devinhorowitz/solar-business-card/docs/solar-glow-drh-v2-mechanical.md

# SOLAR-GLOW · DRH — As-Built Mechanical Reference (v2-era; v3.0 deltas inline)

> **The v3.0 board files this doc names are no longer in `PCB/`** _(removed 2026-07-28; the current
> board is v4.0)_. They stay in git history —
> `git log --diff-filter=D -- PCB/solar-glow-drh-v3_0.kicad_pcb`, then
> `git show <sha>^:PCB/solar-glow-drh-v3_0.kicad_pcb`. The `enclosure/solar-glow-drh-v4_0-backshell-*`
> files are **not** affected by that PCB culling: they are still current and still what goes to the
> fab. _(They were named `…v3_0-backshell-…` until the 2026-08-19 rename; same geometry.)_

> **Superseded for the enclosure — read the v3.0 deltas.** The authoritative shell spec is now
> `enclosure/README.md` and the generator `enclosure/solar-glow-drh-v4_0-backshell-0p6b-brace-cad.py`; the board
> is **v3.0** (`PCB/solar-glow-drh-v3_0.kicad_pcb`). Since this doc was written the shell was built
> and aligned: the **mounting holes moved** (v3.0 positions below), the **floor is 1.00 mm** (0.95
> under a small U2 relief pocket), the **ribs are removed** (a resin diffuser brace carries center
> support), and the **overall height is 3.55 mm**.
> Use this doc for the board envelope, keepouts, and programming access; defer to `enclosure/README.md`
> for every shell number.

Every board dimension and coordinate here is read from the committed KiCad board (KiCad frame:
origin top-left, X across the 50.8 mm width, Y down the 88.9 mm length). Heights are datasheet
figures for the populated parts.

The board changed materially from the *original* shell modeled in `enclosure/` — **four supercaps
instead of two, no edge castellations, VQFN-28 not QFN-20, and an accelerometer tap instead of a
button.** That redesign is done: the shell (`solar-glow-drh-v4_0-backshell-*`, `v3_0`-named until
2026-08-19) is the result.
§8 lists what changed.

---

## 1. Board envelope

- **50.80 × 88.90 mm**, **0.6 mm** FR4, ENIG finish, matte-black soldermask.
- Rounded rectangle, **corner radius 3.0 mm** on all four corners (verified from Edge.Cuts).
- Front face is the show side (naked); the cover is a **back-only shell** that hugs the populated
  rear and presses over the board edge.

## 2. Mounting (4× M2)

Four plated through-holes, **2.2 mm drill**, all tied to **GND**:

| Hole | (x, y) |
|---|---|
| MH3 | (3.0, 3.0) |
| MH4 | (47.8, 3.0) |
| MH1 | (3.0, 85.9) |
| MH2 | (47.8, 85.9) |

All four corners, inset **3.0 mm from both edges** (v3.0 — concentric with the r3.0 corner fillets; was 3.5 mm from the long edges), pitch 44.80 × 82.90. The screws tie
the metal body to GND (intended — the shell becomes a grounded shield). M2 wants 3–4 mm of thread
engagement, so the **bosses must rise the full cavity height**; a thin floor cannot tap.

## 3. Which side is what

- **FRONT (naked, stays exposed):** the two solar cells, the central glow window (DRH monogram),
  and the four corner mount-hole entries. The shell does not cover the front.
- **BACK (the shell hugs this):** everything else — 4 supercaps, MCU, balancer, accelerometer,
  clamp, diodes, LEDs (reverse-mount), passives, the solder-bridge selectors, and the flat
  programming / breakout pads.

## 4. Front face — keep clear

| Feature | Center (x, y) | Size |
|---|---|---|
| PV1 solar cell | (25.4, 17.0) | ≈42 × 23 mm (SM141K06TF) |
| PV2 solar cell | (25.4, 71.9) | ≈42 × 23 mm |
| Glow window (DRH monogram) | (25.4, ~43.9) | x 14.95–35.85, y 40.8–47.0 (≈20.9 × 6.2 mm) bare-FR4 light window |

The two cells take the two ends; the glow window is dead center, backlit from the rear. Nothing on
the front is covered by the shell.

## 5. Back-side height stack (what the cavity must clear)

Two parts set the cavity; everything else clears under it.

| Part | What | Height | Center (x, y) |
|---|---|---|---|
| **U2** | balancer, SOIC-8 | **~1.75 mm (tallest)** | (28.5, 37.0) |
| **SC1–SC4** | WS17 supercaps | **1.7 mm** | see §6 |
| D1, D9 | blocking Schottky | ~1.1 mm | (44.0, 43.9), (43.5, 53.5) |
| U4 | TLV3011, SOT-23-6 | ~1.1 mm | (43.0, 49.0) |
| U3 | accelerometer, LGA-12 | ~1.0 mm | (20.0, 35.9) |
| U1 | MCU, VQFN-28 (4×4) | ~0.9 mm | (9.5, 40.9) |
| D2–D5 | LEDs, LA P47F (reverse-mount) | ~0.83 mm | row at y 43.9 |
| R / C | 1206 / 0805 | 0.6–0.7 mm | central band, y 32–55 |

→ The v3.0 shell uses a **general cavity of 1.80 mm** (cap-limited by the four 1.70 mm supercaps),
with a **0.05 mm relief pocket under U2** (1.75 mm) so the tallest part keeps its air while the floor
stays 1.00 mm — a *different* pocket than the old thin-skin one, and for a different reason
(engraving-stock floor, not a U2-limited cavity). See `enclosure/README.md`. **No through-hole
headers exist** (every connector is flat SMD), so nothing else stands
proud; the stack really is U2/cell-limited.

## 6. Big-part placement (what the shell works around)

**Supercaps — the area hogs** (4 × 28.5 × 17 mm ≈ 43% of the board), long axis along the 88.9 mm
length:

- **Top pair:** SC1 (15.5, 16.9), SC2 (35.3, 16.9) — occupy roughly x 7–44, y 2.6–31.2.
- **Bottom pair:** SC3 (15.5, 72.0), SC4 (35.3, 72.0) — occupy roughly x 7–44, y 57.8–86.3.

**Central electronics band (y ≈ 31–58):** MCU (U1, left), balancer (U2, center), accelerometer
(U3), clamp (Q1/U4/R7-9, right), the LED row + monogram (center), the SW2/SB/SJ selectors, the
passive field, and the breakout pads. This band is where all the routing and the optical heart live.

**Corners** (x 3.0 / 47.8, y 3.0 / 85.9): the four M2 holes (v3.0 positions), clear of the cells.

## 7. Optically-active zone — no pillars here

The LED row (D2–D5 at y 43.9) plus the glow window (x 15–36, y 40.8–47) is the optical heart.
Reverse-mount LEDs sit on the back and emit *through* the board to the front monogram, so an opaque
back shell behind them does not block the glow. But: **do not land support pillars on the LED pads
or the monogram traces**, and clear the ~0.83 mm LED bodies. Treat **x 15–36 / y 40–47 as a
no-pillar keepout**.

## 8. What changed from the shell in `enclosure/` (redesign, don't patch)

- **Four supercaps, not two.** The old CAD models one top pair plus a U2 pocket. v2.1 has four cells
  (both ends, §6). The pocket field, the SC pockets, and the pillar map must be re-laid-out for the
  four-cell footprint.
- **No edge castellations.** Verified: zero pads within 1.5 mm of the rim. The old CAD's biggest
  electrical hazard — press-fit walls shorting the right-edge VS/SDA/SCL castellations — **is gone.**
  Walls can press over the bare-FR4 edge with no edge-pad short.
- **U2 relief pocket (v3.0).** A 0.05 mm pocket under U2 lets the general floor run 1.00 mm while U2 keeps its 0.10 mm air; general cavity 1.80 mm. (Not the old U2-limited thin-skin pocket.) See `enclosure/README.md`.
- **VQFN-28, not QFN-20** (height-irrelevant at 0.9 mm; noted for accuracy).
- **No button.** The actuator is the accelerometer tap, which the metal back-plate *transmits*. No
  dome, no button hole, no cap-touch window.

## 9. Grounding & isolation (still applies)

The four M2 screws ground the body, so it is a defined-potential shield — good — but **any non-GND
copper the metal touches is a short.** Edge castellations are gone (§8), so the wall hazard is moot.
The remaining hazard is **support pillars pressing on the back**: soldermask (~20 µm) is a weak
insulator under load, and any exposed copper (untented vias, the VS pour) shorts to the GND body.
**Land pillars / lip on GND pour or bare laminate** — which the v3.0 shell does: its contacts land on
bare laminate (verified against the PCB), and the perimeter lip / back-frame was narrowed **1.50 →
1.00 mm** to clear the JP1/TP1 bench pads at the right edge. The **die-cut Kapton (~0.05 mm)** blanket
is therefore **dropped**, kept in reserve only for a future board that puts copper under a shell contact.

## 10. Programming access

The **TC2030** Tag-Connect pads (TC1) are on the **back** at (13.3, 16.9), tucked beside SC1, with
NPTH alignment/leg holes; pogo flashing is from the back. Decide up front: **flash before closing
the shell** (the pads sit in the program-before-mount dead space between the cells), or **cut a
TC2030 window** in the back shell for field re-flash. The backup UPDI header J1 (4.7, 38.4) is also
back-side flat pads.

## 11. Variants and open axes (the "enclosure(s)")

- **Material:** **Ti-6Al-4V Grade 5**, single material (yield ~880 MPa). The earlier 7075-T6 fallback
  is dropped — titanium's strength is what lets the floor run thin.
- **Machining (v3.0):** **fully 3-axis CNC-milled** (the photochemical-etch idea is dropped),
  bead-blast finish. **1.00 mm floor** (0.95 under the U2 relief pocket), no ribs — a resin diffuser
  brace carries center support; the window is backed by the brace's white diffuser face (reflector
  frame dropped); overall height 3.55 mm. Full CAD,
  callouts, and fab notes are in `enclosure/README.md`.
- **Floor thickness:** one shipping floor (**1.00 mm**, on the 0.6 mm board); the old 0.55 / 0.75 /
  standard / 0.2 mm-skin variants are retired. The floor is the single value re-issued to PCBWay's minimum.
- **Open vs enclosed:** with no castellations, the old "enclosed variant drops the edge bus"
  complication disappears — the enclosed build is simpler than it was.

## Cross-references

- **Shell design rules, material, machining, CAD knobs:** `enclosure/README.md`.
- **Why four cells / the rear real-estate logic / energy model:** `solar-glow-drh-design-notes.md` §4.
- **Exact pad and keepout geometry:** open `solar-glow-drh-v3_0.kicad_pcb` in KiCad.
