devinhorowitz/solar-business-card/docs/solar-glow-drh-v2-hardware.md

# SOLAR-GLOW · DRH — As-Built Hardware & Wiring Reference (v2-era; v3.0 deltas inline)

> **The v3.0 files this doc names are no longer in `PCB/`** _(removed 2026-07-28; the current board
> is v4.0)_. They are not lost — every revision stays in git history. To read one:
> `git log --diff-filter=D -- PCB/solar-glow-drh-v3_0.kicad_pcb` for the commit that removed it, then
> `git show <sha>^:PCB/solar-glow-drh-v3_0.kicad_pcb`. Nothing below is edited for v4; this is a
> historical record and the filenames are part of it.

> **v2-era doc — read the v3.0 deltas.** Written for v2.1 (+ the v2.2 NFC add). The current board is
> **v3.0 (2-layer)**; `PCB/solar-glow-drh-v3_0.kicad_pcb` governs and `firmware/README.md` carries the
> working pin map. Two v3.0 changes are applied inline here: the **LDRV/LED pin map was permuted**
> (pin 1/PA3 = LDRV1 → D2 … pin 26/PA0 = LDRV4 → D5 — the fan untangle), and the **stackup is 2-layer**
> (GND = full-board B.Cu pour, VS = routed B mesh; no inner planes), and the **NFC power-gate is now committed** (`U6` TPS22918 + `R14` 100 k `NFC_EN` pulldown — see the NFC note below). Net list, PORTMUX, and register
> values carry forward unchanged.

**The single source of truth for firmware.** Every line here is taken from the committed
`solar-glow-drh-v3_0.kicad_pcb` / `.kicad_sch` and cross-checked against the
AVR64DD32-28 datasheet (DS40002315), the ADXL367 datasheet, and the
SM141K06TF and SCPC parts. Where a register value is given, it is the value the firmware must
write to match what is physically routed.

**NFC subsystem — now fully committed (v2.2 → v3.0).** The board carries the NFC tag subsystem
(`U5` NT3H2211, `C8`, `C9` DNP, `R13`, and the etched antenna coil) on **PA6** (field-detect),
the **high-side load switch `U6` (TPS22918, SOT-23-6)** that power-gates `U5`'s VCC (`VNFC`)
from **PA7** (`NFC_EN`), and — added in the v3.0 R14 patch — a **100 kΩ pulldown `R14`** that
holds `NFC_EN` low whenever PA7 tristates (UPDI, reset, brown-out). All of it is committed on
`solar-glow-drh-v3_0.kicad_pcb`, and the NFC net wiring below has been **verified off the board
copper**: FD→PA6 ✓, `NFC_EN`→U6.ON ✓, `U5` Vcc→`VNFC` = U6.VOUT ✓, `R13`→VS (the always-on
rail, not the switched one) ✓, `R14` `NFC_EN`→GND ✓. The **U6 pin map is now verified against TI SLVSD76C (TPS22918 Rev C, then committed at
`datasheets/U6  TPS22918DBVR  $0.55.pdf` — culled 2026-08-01 with the other replaced-part sheets, git history; the doc for the then-ordered DBVR part; the -Q1 automotive
twin SLVSCZ8B has an identical pin table)** — and the check caught a real defect: the symbol had
**VIN/VOUT and GND/QOD transposed** (board said 1=VOUT, 2=QOD, 5=GND, 6=VIN; only ON=3 and
CT=4 were right). As routed it would have left U6 with no ground and fed VS into VOUT.
**Fixed on the board 2026-07-02**: pads renetted to TI truth (1=VIN, 2=GND, 3=ON,
4=CT-float, 5=QOD, 6=VOUT), schematic pin numbers corrected, QOD strapped to VOUT (internal
R_PD ≈ 25 Ω discharge — a TI-sanctioned config), CT left floating (also sanctioned), and the
local copper reworked to match. One open item: the **FD wake is bench-pending**
(scope PA6 on a real phone tap with VCC gated off). The NT3H2211 register/memory facts are
verified against the NTAG I²C plus datasheet (NT3H2111_2211 Rev 3.6).

MCU: **AVR64DD28**, 28-pin VQFN (footprint `solarglow:U1`). It sits on the **back** of the board.

---

## 1. MCU pin map (complete, as routed)

| Pad | Pin | Net | Function | Peripheral / firmware note |
|----:|---|---|---|---|
| 26 | **PA0** | `LDRV4` | LED (D5) cathode drive | **TCA0 WO0** — low-side sink, 150 Ω ballast |
| 27 | **PA1** | `LDRV3` | LED (D4) drive | **TCA0 WO1** |
| 28 | **PA2** | `LDRV2` | LED (D3) drive | **TCA0 WO2** |
| 1  | **PA3** | `LDRV1` | LED (D2) drive | **TCA0 WO3** |
| 2  | **PA4** | `PA4` | spare GPIO | spare (JP2 removed in v3.0 — no breakout) |
| 3  | **PA5** | `BTN` | reserved button | GPIO; only routed to a stub (the one DRC `track_dangling`); v3 hook |
| 4  | **PA6** | `FD` | NFC field-detect in (`U5`) | PORTA pin int, **falling**; field-powered (works VCC-off, §8.4); int pull-up on + ext 10k (`R13`) to VS — *v3.0-committed (R13→VS verified on copper); bench: scope a real tap* |
| 5  | **PA7** | `NFC_EN` | NFC VCC load-switch enable | output, **active-HIGH**, LOW = NFC off (default); **ext 100 k pulldown `R14` (v3.0)** holds it off while PA7 floats — *committed; U6 pin map verified per TI SLVSD76C, defect found + fixed 2026-07-02* |
| 6  | **PC0** | `PC0` | spare GPIO | spare (JP2 removed in v3.0) |
| 7  | **PC1** | `PC1` | spare GPIO | spare (JP2 removed in v3.0) |
| 8  | **PC2** | `SDA` | I²C data | **TWI0 host SDA** via `TWIROUTEA = ALT2`; 4.7 kΩ pull-up to VS |
| 9  | **PC3** | `SCL` | I²C clock | **TWI0 host SCL** via `TWIROUTEA = ALT2`; 4.7 kΩ pull-up to VS |
| 10 | **VDDIO2** | `VDDIO2` | PORTC I/O supply | tied to VS by SJ1 (0 Ω) — see §5 |
| 11 | **PD1** | — | free | unconnected (AIN1) |
| 12 | **PD2** | `VSENSE` | light / rail sense | **AIN2 (ADC)** + **AINP0 (AC0+)** → wake-on-light (§6) |
| 13 | **PD3** | — | free | unconnected (AIN3 / AINN0) |
| 14 | **PD4** | — | free | unconnected (AIN4) |
| 15 | **PD5** | — | free | unconnected (AIN5) |
| 16 | **PD6** | — | free | unconnected (AIN6 / AINP3 / DAC VOUT) |
| 17 | **PD7** | — | free | unconnected (VREFA / AIN7) |
| 18 | **VDD** | `VS` | core supply | the clamped rail, ≤ 3.60 V worst-case (≈3.50 typ) |
| 19 | **GND** | `GND` | ground | |
| 20 | **PF0** | `INT2` | accel INT2 input | PORTF pin interrupt |
| 21 | **PF1** | `INT1` | accel INT1 input | PORTF pin interrupt |
| 22 | **PF6/RST** | — | free | defaults to RESET; fuse to GPIO if ever needed |
| 23 | **UPDI** | `UPDI` | programming | TC2030 pad (TC1) + backup header J1 |
| 24 | **VDD** | `VS` | core supply | |
| 25 | **GND** | `GND` | ground | |
| EP | — | `GND` | exposed pad | thermal + ground |

**LED ↔ channel map** (note the off-by-one: D1/D9 are Schottkys, not LEDs):
`D2 → LDRV1 → PA3/WO3`, `D3 → LDRV2 → PA2/WO2`, `D4 → LDRV3 → PA1/WO1`, `D5 → LDRV4 → PA0/WO0` (v3.0 fan untangle).
Each LED: anode → `ANODE` (common) → **SW2** → VS; cathode → `Kn` → ballast (150 Ω) → `LDRVn` → MCU pin.

---

## 2. Nets & rails

| Net | What it is |
|---|---|
| `VIN` | PV1 (+) solar node, **before** blocking diode D1. ~0 V in the dark, rises with light. Feeds the VSENSE divider, D1 anode, and D10 (clamp-supply OR). |
| `VINB` | PV2 (+) solar node, before blocking diode D9, and D11 (clamp-supply OR). |
| `VS` | The storage rail (after D1/D9). = MCU VDD, accel VDD, LED anode source, supercap top. **Clamped ≤ 3.60 V worst-case** by the TLV3011 comparator + PNP shunt (U4/Q1). |
| `GND` | Ground — **full-board B.Cu pour** (`GND_B`) in v3.0 (was the In1 plane in v2.3), EP, the four M2 mount holes. |
| `MID` | Supercap series midpoint, balanced by U2 (ALD910025 dual SAB). |
| `CLBASE` / `CLREF` | Clamp internals — Q1 base (U4 open-drain OUT + R9 pullup) / VS sense-divider tap into U4 IN−. |
| `VCMP` | Clamp-comparator supply — **VIN OR-ed with VINB** through Schottkys D10/D11. Powers U4 only while a panel produces (0 draw in the dark); diode-OR so either panel alone keeps the clamp live under split shade. |
| `ANODE` | Common LED-anode node, switched by SW2. |
| `TINY` | Dim-mode node: LED anodes → VS through R12 (220 Ω) when SW2 = TINY. |
| `LDRV1‒4` | LED cathode drives → MCU PA0‒PA3. |
| `K2‒K5` | Individual LED-cathode-to-ballast nets. |
| `SDA` / `SCL` | I²C bus (accel `0x1D` + NFC tag `0x55`); tapped at `JP1.4`/`JP1.3` on the bench strip. |
| `INT1` / `INT2` | Accel interrupt lines → PF1 / PF0. |
| `VSENSE` | Light/rail sense → PD2. = VIN/2 (R5/R6 = 1 MΩ each), filtered by C5 (10 nF). |
| `PA4` / `PC0` / `PC1` | Spare GPIO (the v2-era JP2 breakout is gone — reserved, un-broken-out). |

Stackup: **v3.0 is 2-layer** (F / B) — GND = full-board B.Cu pour, VS = routed B mesh; 0.6 mm. (v2.3 fallback: 4-layer, F · In1 GND · In2 VS · B. v2.1 was 6-layer.)

---

## 3. Peripheral setup cheat-sheet (what firmware must configure)

**These are not defaults — they are the settings that match the routing.**

- **LED PWM — TCA0, split mode.**
  Keep `PORTMUX.TCAROUTEA = DEFAULT` (WO0‒WO3 already land on PA0‒PA3). Run TCA0 in
  **split mode** to get six 8-bit channels; WO0‒WO3 are the four LEDs, each with independent
  duty and a shared period. Set PA0‒PA3 as outputs. The 150 Ω ballast fixes the **peak**
  current (~9 mA on the clamped rail); PWM only trims the **average** below that, so brightness
  can be set freely but cannot exceed the ballast ceiling.
  *Gotcha:* the LEDs only light if **SW2 is bridged ON or TINY**. If SW2 = OFF (unbridged),
  no PWM will produce light — that's the hardware master switch.

- **I²C — TWI0, host mode.**
  **`PORTMUX.TWIROUTEA = ALT2`** (puts host SDA/SCL on PC2/PC3 — the default routes to
  PA2/PA3, which are LED pins). External 4.7 kΩ pull-ups are fitted, so don't enable internal
  ones. Bus is the accelerometer (`0x1D`) — and, since **v2.2**, the
  NFC tag `U5` (`0x55`); the two addresses don't clash, so no firmware change beyond
  talking to both. `U5` is reachable on I²C only while `NFC_EN` (PA7) powers it — it is
  gated **off** by default. FD (a pin interrupt on PA6) is separate from the bus, and is
  field-powered, so it works even with `U5`'s VCC gated off.

- **Accelerometer wake — PORTF pin interrupts.**
  Configure **PF1** (INT1) and **PF0** (INT2) as inputs with edge interrupts to match whatever
  the ADXL367 INT pins are programmed to assert (tap, double-tap, activity). These are the
  wake source for tap-to-glow.

- **Light sense / wake-on-light — PD2.**
  PD2 is both **AIN2** (ADC) and **AINP0** (AC0 positive input). See §6 for the validated
  options. The divider is VIN/2, so the ADC reading is `2 × VSENSE` ≈ VIN.

- **Free expansion ADC/analog** (all unconnected, available): PD1 (AIN1), PD3 (AIN3/AINN0),
  PD6 (AIN6/AINP3/DAC out), PD7 (VREFA/AIN7).

---

## 4. Devices on the board

**U3 — ADI ADXL367 accelerometer (the actuator; replaces the LIS2DH12 on backorder).**
- Interface: **I²C** (SCLK, pin 1 → GND = I²C mode). SDA = pin 2, SCL = pin 4.
- **Address: `0x1D`** 7-bit (ASEL, pin 3 → GND). 8-bit: write 0x3A / read 0x3B. IDs: DEVID_AD (0x00)
  = 0xAD, PART_ID (0x02) = 0xF7 (DEVID_MST 0x01 also reads 0x1D, coincidental with the bus address,
  not the same thing).
- Interrupts: **INT1 (pin 5) → PF1** (tap), **INT2 (pin 6) → PF0** (activity). Strapping is frozen
  in the schematic/PCB/BOM as of the ADXL367 swap.
- Supply Vs/Vsupply → VS; SCL → PC3, SDA → PC2 (MCU side); SDA/SCL pull-ups R10/R11 to VS. Decoupled by C6.
- Role: tap / double-tap / activity → INT → wakes the MCU. A tap is vibration, so the metal
  back-plate transmits it in the enclosed build. Single-vs-double tap is resolved in the
  ADXL367's own hardware window; the firmware reads STATUS_2 once (see `firmware/README.md`).

**U5 — NXP NT3H2211 (NTAG I²C plus, 2 KB) — NFC contact tag (v2.2).**
- Interface: **I²C target, address `0x55`** 7-bit (write 0xAA / read 0xAB); shares the TWI0
  bus with the accel (0x1D), no clash.
- **FD (field detect, pin 4) → PA6**, open-drain, ext 10 kΩ (`R13`) to VS: idles HIGH, pulls
  LOW on an NFC field → PA6 falling-edge interrupt wakes the MCU. FD is **field-powered**
  (§8.4), so this works even with `U5`'s VCC gated off; firmware also enables PA6's internal
  pull-up.
- Supply Vcc → **`VNFC` = `U6` (TPS22918) output**, gated by `NFC_EN` (PA7, active-HIGH; `R14` 100 k pulldown); U6 itself draws ISD ≈ 0.5 µA typ (3.5 µA max) from VS while off and IQ ≈ 8.3 µA while on (SLVSD76C §6.5); the
  switch input is on VS (clamped ≤ 3.60 V worst-case, inside the 3.6 V max). **Off by default** to kill
  the ~195 µA idle draw (datasheet Table 42); only powered around an MCU↔tag I²C access. `C8`
  (100 nF) decouples the switched VCC; `VOUT` (energy-harvest output) unconnected.
- Antenna: PCB coil on `LA`/`LB`, tuned to 13.56 MHz by the chip's internal 50 pF
  (`C9` = DNP trim). No firmware involvement in the radio.
- Role: a phone tap reads a contact **vCard** (RF-powered, so it reads with the cap flat) and
  the FD line wakes the glow. Firmware: `nfc.c` writes the NDEF into user memory from block 1;
  the factory CC (`E1 10 6D 00`) is left in place — block 0 is never written, as that would
  change the I²C address. *Net wiring verified off the v3.0 board copper (see the header note); FD-wake scope check still open.*

**LEDs — 4× ams OSRAM LA P47F (amber, reverse-mount).** Low-side driven on PA0‒PA3 (§1/§3),
150 Ω ballast each, anodes commoned to `ANODE` and switched by SW2.

**SW2 — LED master selector (3-pad solder bridge).** `ANODE` common; bridge to **VS = ON**
(full), to `TINY` = **TINY** (anodes → VS via R12 220 Ω, dim/long-runtime), unbridged = **OFF**
(true hardware off). Also `SB1‒SB4` are per-LED disable bridges in series with each ballast.

**Breakouts / programming.**
- `TC1` — TC2030 Tag-Connect (UPDI): hands-free flashing. `J1` — backup UPDI header.
- The v2-era `JP1`/`JP2` 2.54 mm breakout headers are **gone in v3.0**; `JP2` has no successor
  (PA4/PC0/PC1 stay reserved, un-broken-out). The `JP1` designator is **reused** for the bench pad
  strip below.

**Bench pad strip — `TP1` + `JP1` (new in v3.0).** Five bare SMD pads (1.7 mm square, ENIG,
2.54 mm pitch) in a column at x 48.4 on the **back**, in the margin between SC2's body edge
(x 43.8) and the card edge — the one strip the Ti shell interior clears (its lip was thinned
1.50 → 1.00 mm for exactly this; closed-shell clearance to the pads is 0.50 mm). Top to bottom:

| Pad | y | Net | Purpose |
|---|---|---|---|
| `TP1` | 12.00 | `VIN` | Solar-input node (pre-D1) — charge test / panel emulation |
| `JP1.1` | 14.54 | `GND` | Return (B.Cu pour) |
| `JP1.2` | 17.08 | `VS` | **Bench power injection** — 3.0–3.3 V, current-limited ~50 mA |
| `JP1.3` | 19.62 | `SCL` | I²C tap (via-in-pad stitches to the F-side run) |
| `JP1.4` | 22.16 | `SDA` | I²C tap (via-in-pad) |

No holes, nothing proud of the mask — clip, pogo, or tack a wire on for a bench session and
wick it off after. **Bench sequence:** inject at `JP1.2`/`JP1.1` → flash via `TC1` → functional
test → supercaps on → charge test at `TP1` → panels last. With the shell off the strip also
gives post-assembly I²C access to the NT3H2211 (`0x55`) and ADXL367 (`0x1D`); with the shell
on nothing is probe-able anyway, by design.

---

## 5. Power & sensing

- **Harvest:** 2× SM141K06TF (Voc 4.15 V, Vmp 3.35 V, Isc 58.6 mA at 1 sun), in parallel,
  each behind its own Schottky — **PV1 → D1 → VS** and **PV2 → D9 → VS** (both MMSD301T1G) —
  so a shadow on one panel can't back-drive the other.
- **Storage:** 4× SCHURTER WS17 (P/N 3-153-438), wired **2P2S → 1 F @ 5.5 V ≈ 15 J**, on one
  node balanced by **U2 (ALD910025)** at the midpoint. Cell rating is **−40 to +85 °C**; each
  cell sees only VS/2 (≈1.75 V, far under the 2.75 V rating), so voltage is never the limit,
  but high heat is: leakage climbs and calendar life roughly halves per 10 °C over 85 °C.
  **Hot-car caveat** — a matte-black card on a sunlit dash can self-heat to 80–90 °C, at/above
  the cell rating; this ages the supercaps and speeds self-discharge (it does **not** damage
  the ICs — see the clamp note). An 85 °C+ / 105 °C cell is the fix if hot storage is a goal.
- **Rail clamp:** **TLV3011 comparator + on-chip 1.242 V ref (U4)** + PNP (Q1) shunt holds
  **VS ≤ 3.60 V worst-case** (≈3.50 V typ) so the accelerometer **and** the NFC tag stay at/under
  their shared 3.6 V operating max. Divider **R7 (6.81 M) / R8 (3.74 M)** sets the trip via
  VS = 1.242·(1+R7/R8); it sits on VS (must — both panels feed VS through separate diodes).
  R7/R8 were chosen to put the **worst-case** clamp (ref ±1% + 100 ppm/°C + resistor ±1%) right
  on 3.60 V, wringing out maximum storage energy (E ∝ V²) while staying under the datasheet max. The divider is high-impedance (6.81 M / 3.74 M ≈ 10.5 MΩ) — the **only** continuous passive drain off the supercaps, ~**0.33 µA** at 3.5 V. This high-Z is only possible because the TLV3011’s ±10 pA input bias makes the resistor offset negligible; the old TLV431’s 0.5 µA Iref would have added ~0.9 V here, which is why it was forced to a low-impedance 1.8 M / 1.0 M divider (≈1.24 µA).
  Open-drain OUT drives Q1 through the R9 pullup. **Comparator power:** U4's V+ is fed from
  **VCMP = VIN OR-ed with VINB** through two Schottkys (D10/D11), **not** from VS — so U4's
  ~2.8 µA quiescent is pulled from the solar cells only while they produce and is **zero in the
  dark** (the clamp can only ever need to act while charging). The OR (vs VIN alone) keeps the
  clamp live under **split illumination** — a shadowed panel can't leave VS unclamped while the
  other charges it. R9, the divider, and Q1 stay on VS (R9 *must*, or Q1 turns on in the dark and
  shorts VS). Safe because the TLV3011**B**'s fail-safe inputs and its output-pullup-independent-
  of-supply rating mean an unpowered U4 (R9 holding Q1's base at VS) neither back-powers nor
  leaks through the chip. **C10** (100 nF) decouples VCMP at U4's V+ — not strictly required (VCMP carries no switching load; the Q1-drive transient sinks from VS through R9, and the comparator has hysteresis), but standard local decoupling. *(Supersedes the earlier TLV431 divider, whose
  0.5 µA Iref across a 1.8 M top resistor pushed the real clamp to ~3.74 V typ / ~4.5 V worst —
  a latent over-voltage the TLV3011's ±10 pA input bias eliminates.)* **Hot-car:** at 85–105 °C
  worst-case creeps to ~3.61–3.65 V, still ~1 V under both parts' 4.6/4.8 V absolute-max damage
  line, so no damage — only a brief excursion outside the guaranteed operating window.
- **VDDIO2 = VS** via SJ1, so PORTC runs at the rail and **MVIO is unused** (no separate I/O
  voltage). The MVIO fuse `SYSCFG1.MVSYSCFG` should be set to **SINGLE** to match (factory
  default is DUAL; DUAL also works since VDDIO2 sits at a valid voltage, but SINGLE is the
  intent). PORTC pins are valid up to VS. See the firmware README "Fuses" section.
- **Sense:** `VSENSE = VIN / 2` (R5/R6 = 1 MΩ, C5 = 10 nF, ~5 ms filter) into PD2. Reads the
  *solar input*, not the stored rail — see §6.

---

## 6. Wake-on-light — validated, viable as wired (no board change)

> **Firmware reconciliation (read first).** The firmware implements **path B
> only**. **Path A (AC0 instant wake) was found non-viable on this silicon** once
> verified against the datasheet: the AC0 interrupt and flags do not update while
> `CLK_PER` is stopped, and Table 13-4 does not list the AC as a Standby or
> Power-Down wake source, so an AC0 wake would silently never fire. The **wiring
> below is still correct** and path B works exactly as described; what is stale is
> the option-A recommendation (AC0 can't wake from Standby on this part). The
> current/darkness estimates have moved twice: the firmware bring-up found the old
> ~2 µA accel figure was really ~10 µA for the click-armed LIS2DH12, and the ADXL367
> swap then dropped it to ~0.89 µA (standby ~2.7 µA). The authoritative wake/power
> model lives in **`firmware/README.md` ("Power notes / wake architecture")**.

Confirmed electrically this revision. The divider sits on **VIN (before D1)**, so VSENSE
collapses to ~0 V in the dark and rises with light; **PD2 = AINP0** is a real AC0 input and
**AIN2** is a real ADC input. Signal swing: ~0 V dark → ~1.2–2.1 V in light (dim-indoor to
sun), against an easily-set threshold near ~0.4 V. AC0 input range is −0.2 V…VDD, so VSENSE
fits. Two implementations, same wiring — choose per use:

**A) AC0 comparator — instant wake. [NOT VIABLE — see the reconciliation note above; kept as the record of why it was considered.]**
- AC0 `MUXPOS = AINP0` (PD2); `MUXNEG = DACREF`; set threshold `DACREF × VREF` ≈ 0.4 V.
- Enable hysteresis (10/25/50 mV) so a flickering source doesn't chatter the interrupt.
- `CTRLA.RUNSTDBY = 1`, sleep in **Standby**; the AC0 CMP interrupt wakes the core the moment
  light appears. Use `CTRLA.POWER = 0x2` (slowest, plenty fast for light) ≈ **~12 µA** standing.
- Dark tolerance (as originally estimated): AC0 (~12 µA) + accel (~2 µA) + standby (~3 µA)
  ≈ ~16 µA. *The AC0 assumption is wrong* — A does not work at all on this part. The accel
  figure has since settled at ~0.89 µA (ADXL367), so total dark standby is ~2.7 µA — see the
  README for the current model.

**B) RTC/PIT poll + ADC — dark-tolerant.**
- Sleep in **Power-Down**; wake every ~1–2 s off the internal-ULP RTC/PIT; ADC-sample PD2
  (AIN2); escalate to full wake only when the reading clears the light threshold.
- Detection latency ~1–2 s. (The "~1–3 µA → ~5–7 days" originally written here omitted the
  always-on accelerometer; with the ADXL367 at ~0.89 µA the standing draw is ~2.7 µA total —
  no longer accel-dominated — so darkness survival is back on the order of **days** — see README.)
- Note: in the deepest Power-Down the AC0 is off, so this is the only wake-on-light that works
  in that mode — and it's the better fit for "card sat in a drawer."

Both recharge instantly when light returns. **B is the baseline and the only viable
wake-on-light path.** Instant response is not lost: the accelerometer's motion/tap interrupt
is a confirmed Power-Down wake source, and picking the card up to carry it into the light *is*
that motion, so A is not needed. A true zero-latency *light* trigger, if ever wanted, is the
supported AC0 → Event System → CCL → CCL-interrupt path (Table 13-4 lists CCL as a Standby
wake source) — a v-next exercise, not built here.

*Open empirical item:* the indoor VIN figures are estimated from the panel's logarithmic
Voc-vs-illumination behavior; the dark (0 V) and sun (datasheet) endpoints are firm. The
energy-budget bench measurement (still the project's #1 gate) will confirm the indoor middle
and set the achievable duty cycle.

---

## 7. Firmware bring-up order

1. **Clocks/power:** set `VREGCTRL.PMODE = AUTO`; pick the main clock (internal OSC, no crystal
   fitted); plan to sleep aggressively (the rail is tiny).
2. **GPIO/PORTMUX:** `TCAROUTEA = DEFAULT`, `TWIROUTEA = ALT2`; PA0‒PA3 outputs (LEDs),
   PF0/PF1 inputs w/ interrupt (accel), PD2 left to the analog peripheral.
3. **I²C up, talk to the accel** at `0x1D`; configure tap → INT1 and activity → INT2;
   verify the PF1/PF0 interrupts fire on a physical tap and on a pickup.
4. **TCA0 split-mode PWM** on the LEDs; **confirm SW2 is ON/TINY** or nothing lights.
5. **Wake-on-light** (§6) — implement path B (deepest sleep, the only viable path); instant
   response to handling comes from the accel interrupt, so A is not built.
6. **Housekeeping:** ADC read of VSENSE (×2 = VIN) and VDD/10 for charge state; optional EEPROM
   activation counter; brown-out behavior around the supercap rail.

**Pins free for new features:** PD1, PD3, PD4, PD5, PD6, PD7, PF6/RST (7 GPIO, most
ADC-capable; PD6 can be a DAC output), plus PA4/PC0/PC1 (spare — no breakout since v3.0) and PA5 (`BTN`)
reserved. (On v2.2, PA6 = NFC `FD` and PA7 = `NFC_EN`.)
