devinhorowitz/solar-business-card/docs/firmware-to-pcb-open-items.md

# Firmware → PCB / Hardware - open cross-team items (SOLAR-GLOW DRH v3.0 - SUPERSEDED by the v4.0 managed-solar redesign; the TLV3011B clamp / Q1 shunt / D1 blocking-diode / VIN-at-clamp scheme this memo relies on was removed. Kept for record only.)

**From:** Firmware
**Date:** 2026-07-10
**Re:** one number we need to finish the in-sun "loading" tell, plus two confirmations

## Where firmware stands
Firmware is code-complete and link-clean — every module symbol resolves, `led.c`
is intact, and it reviews warning-free. It has **not** been through a real AVR-Dx
build + bench yet; that gap is on us (toolchain / DFP), not you.

> **Update 2026-07-10:** the one number below (VIN at the clamp) has since been
> derived and the in-sun sweep is now **wired** (VIN ≥ 3.60 V, `USE_SUN_SWEEP=1`).
> See the **RESOLVED** banner in §1. This memo is kept for the derivation record and
> for the two confirmations in §2–§3.

---

## 1. Primary ask — VIN at the clamp point (for the in-sun sweep)

> **RESOLVED 2026-07-10 (PCB → firmware).** VIN at the clamp = **≥ 3.60 V**, wired.
> When the caps top out [v3 mechanism - REMOVED in v4] in v3 the TLV3011B (U4) held VS at ~3.50 V and Q1 shunted the excess. v4 deletes U4/Q1/D1 and the whole clamp-shunt scheme: the merged panel node SRC feeds the AEM10300 (U8) MPPT buck-boost harvester, the supercap tank STO floats unclamped (0.2–4.65 V), and VS is the regulated 3.3 V output of the TPS7A0233 LDO (U9);
> VIN then rides one blocking-diode drop above that, self-settling between VS (~3.50 V,
> as Vf→0) and panel Voc (4.15 V, as current→0) and never above Voc — the naive
> "VS_trip + Vf(Isc)" over-predicts because MMSD301T1G is a high-Vf *signal* Schottky
> and the panel cannot source full Isc that far up its knee. 3.60 V sits above the held
> VS (⇒ real forward current through D1 = genuine sun, not just a full cap) yet below
> Voc, and far above indoor light (VIN ~0.8–2.1 V). Firmware wired it as
> `SWEEP_SUN_VIN_MV = 3600` (board.h, folded to 2950 ADC counts), with the independent
> caps-full safety gate `SWEEP_CAPS_FULL_MV = 3300` and a `USE_SUN_SWEEP` master flag.
> The original ask is kept below for context.

We have an optional UX "tell": in **strong sun with the caps full**, the card
plays a left→right "loading" sweep across the DRH LEDs (`led_sweep`, already
written and tuned). It only ever runs when the caps are *already* full, so it
can't drain the pack — it just spends free solar. The **trigger is the only
missing piece**, and it needs one threshold from you.

**What we need:** the value of **VIN — the solar-node voltage on the panel side
of net SRC - there is no blocking diode D1 in v4; the merged panel node SRC is what R5/R6 (1 MΩ each) divide into PD2 as VSENSE -** *when
the TLV3011B clamp is actively holding VS at its trip point under strong sun.*

- Firmware reads this as `sense_vin_mv()` ( = the PD2 reading × 2 ), in millivolts.
- You've [REMOVED in v4 - no clamp, no TLV3011B (U4); VS is the fixed 3.3 V TPS7A0233 LDO (U9) output and the supercap tank STO is sensed separately on STO_SNS/PD1] re-anchored the (removed) clamp to the TLV3011B at **VS ≈ 3.5 V nominal /
  3.60 V worst case.** Assuming that's firm, we want the **corresponding VIN** at
  that operating point. Our rough placeholder is ~3.9 V (VS + a Schottky drop
  across D1) — but we don't want to ship a guess. Please give us the real figure
  from the board / sim.
- If you can, give us **two points**: VIN as the clamp *just* begins to engage,
  and VIN under *hard* clamp in bright sun. That spread lets us set the threshold
  with sensible hysteresis so the sweep doesn't chatter at the boundary.

**Why the exact number is feel-critical, not safety-critical:** the sweep's hard
safety gate is `sense_vdd_mv() ≥ 3300 mV` (caps full), measured against the supercap tank STO - in v4 sense_vdd_mv() reads STO via STO_SNS (PD1, ÷3), not VS, which is now the constant 3.3 V LDO rail - and
**independent of the clamp**. Even if the VIN figure is a little off, the
animation can never drain the pack — your number only sets *when in the sun* it
kicks in, i.e. how it feels.

---

## 2. Please confirm - [OBSOLETE in v4] the Q1 thermal fix no longer applies - Q1 (the v3 BCP5316 shunt transistor) was deleted in the AEM10300 managed-solar redesign, so there is no Q1 dissipation to manage. (The 150 Ω LED ballast R1–R4 is unchanged, so firmware's ballast assumption still holds.)

Our understanding: Q1's over-temp is being fixed **on the copper** — solid
pad-3-to-pour, a GND thermal-via cluster, and a top-side GND flood over Q1
(θ_JA ~206 → ~90 °C/W, bringing Q1 in spec at full 385 mW across the hot-car
range) — and the **45 Ω ballast swap stays shelved.**

If that's still the plan, **firmware keeps the 150 Ω ballast assumption and ships
no brightness retune and no cap-drain interlock** (the interlock only ever
existed to guard a firmware power-dump we are no longer doing). Please flag us if
the ballast or pour plan changes — that's the one thing that would force a
firmware brightness/interlock rework.

---

## 3. Minor — C13 footprint field mislabel (non-electrical)

> **RESOLVED.** C13's footprint field now reads `solarglow:C13` in the schematic; the
> stale `solarglow:C7` is gone. Left here for the record.

Heads-up for your next schematic touch: **C13**'s footprint *field* reads
`solarglow:C7`, while the reference designator itself is correctly "C13". No
electrical impact — just a stale field to correct while you're in there.

---

## Appendix — ADC conversion (for sanity-checking your numbers)
12-bit ADC against the **2.500 V** internal reference:

| Path | Formula | Example |
|---|---|---|
| **SRC** (VSENSE = SRC/2 on PD2) | `counts = VIN_mV × 0.8192` | VIN 3.90 V → 3195 counts (valid to VIN 5.00 V, where pin = 2.5 V = ref) |
| **VDD / VS** | `counts = VDD_mV × 0.16384` | VS 3.30 V → 541 counts |

So whatever VIN you hand us, we can convert straight to the compare value the
poll loop tests. The number we ultimately drop into `board.h` is
`SWEEP_SUN_VIN_MV` (name TBD), in millivolts at the VIN node.
