devinhorowitz/solar-business-card/Generated/fabdocs/solar-glow-drh-v4_0-handbuy.md

# Hand-buy list — SOLAR-GLOW DRH v4.0 (1 board)

GENERATED by `scripts/bom_split.py` — do not edit. Everything here is bought by
**you**, not by PCBWay: the deliberately hand-soldered parts plus the items that
never reach a pick-and-place.

| Ref(s) | Qty | MPN | Manufacturer | Supplier | Distributor P/N | What |
|---|---|---|---|---|---|---|
| PV1, PV2 | 2 | `SM141K06TF` | ANYSOLAR | DigiKey | 2994-SM141K06TF-ND | SM141K06TF |
| SC2, SC4 | 2 | `3-153-438` | SCHURTER | Mouser | 693-3-153-438 | WS17 1F 2.75V |
| SC1, SC3 | 2 | `3-153-440` | SCHURTER | Mouser | 693-3-153-440 | SS17 1.8F 2.75V |
| FER1 | 1 | `364006` | Würth Elektronik | Mouser | 710-364006 | Wurth WE-FSFS ferrite sheet behind the coil -- load-bearing for the NFC tune |
| HW1 | 8 | `DIN 84 M2x3 brass` | — | — | — | shell screws for the MAX shell (stack 3.40), one per mount; any DIN 84 M2x3 -- source locally, not a distributor line |
| HW2 | 8 | `ISO 7045 M2x2 A2/A4` | — | — | — | shell screws for the LITE shell (stack 2.42; an M2x3 tip stands 0.58 proud) -- source locally, not a distributor line |
| HW3 | 8 | `ISO 7045 M2x1.6 A4/316` | — | — | — | frame screws for the AIR frame (stack 1.80; tip hides 0.20 in the boss spotface, 1.0 mm engagement in 316 -- fine for a frame clamping a 6 g card) -- micro-fastener houses stock M2x1.6; source with the frame |
| INS1 | 1 | `polyimide film 0.05 mm` | — | — | — | insulator; cut from stock film -- not a distributor line |

**Bought once for the project, not per board:**

| Ref | Qty | MPN | Manufacturer | Supplier | Distributor P/N | What |
|---|---|---|---|---|---|---|
| PRG1 | 1 | `5879` | Adafruit | Mouser | 485-5879 | Adafruit UPDI Friend. 5879 is Adafruit's OWN product number, not a distributor P/N -- a cart upload of the bare MPN finds nothing; Mouser resolves 485-5879 (DigiKey would be 1528-5879-ND, dry as of 2026-08-02). Substitute if this one goes dry too: the HV variant, which does standard UPDI as well -- see SUBS in BOM/check_stock.py. |
| CBL1 | 1 | `TC2030-MCP` | Tag-Connect | — | — | Tag-Connect TC2030-MCP, the LEGGED cable. Deliberately NOT a cart line: DigiKey stocks only the legless TC2030-MCP-NL and the legged part is zero/restricted at Mouser, so order it from Tag-Connect direct. Emitting it into a cart CSV would just fail at upload, or worse, silently buy the wrong cable. |

**Ordered, but not from a distributor:**

- `ENC1` — the titanium back-shell -- its own fab order, machined from enclosure/*.step

**The supercaps are two different parts.** SC1/SC3 and SC2/SC4 are different
capacitances with different MPNs and separate stock pools; four of either one
builds nothing. Consistency check [15] holds this list against the board.
