devinhorowitz/solar-business-card/enclosure/solar-glow-drh-frame-air-316L-DRAWING.pdf

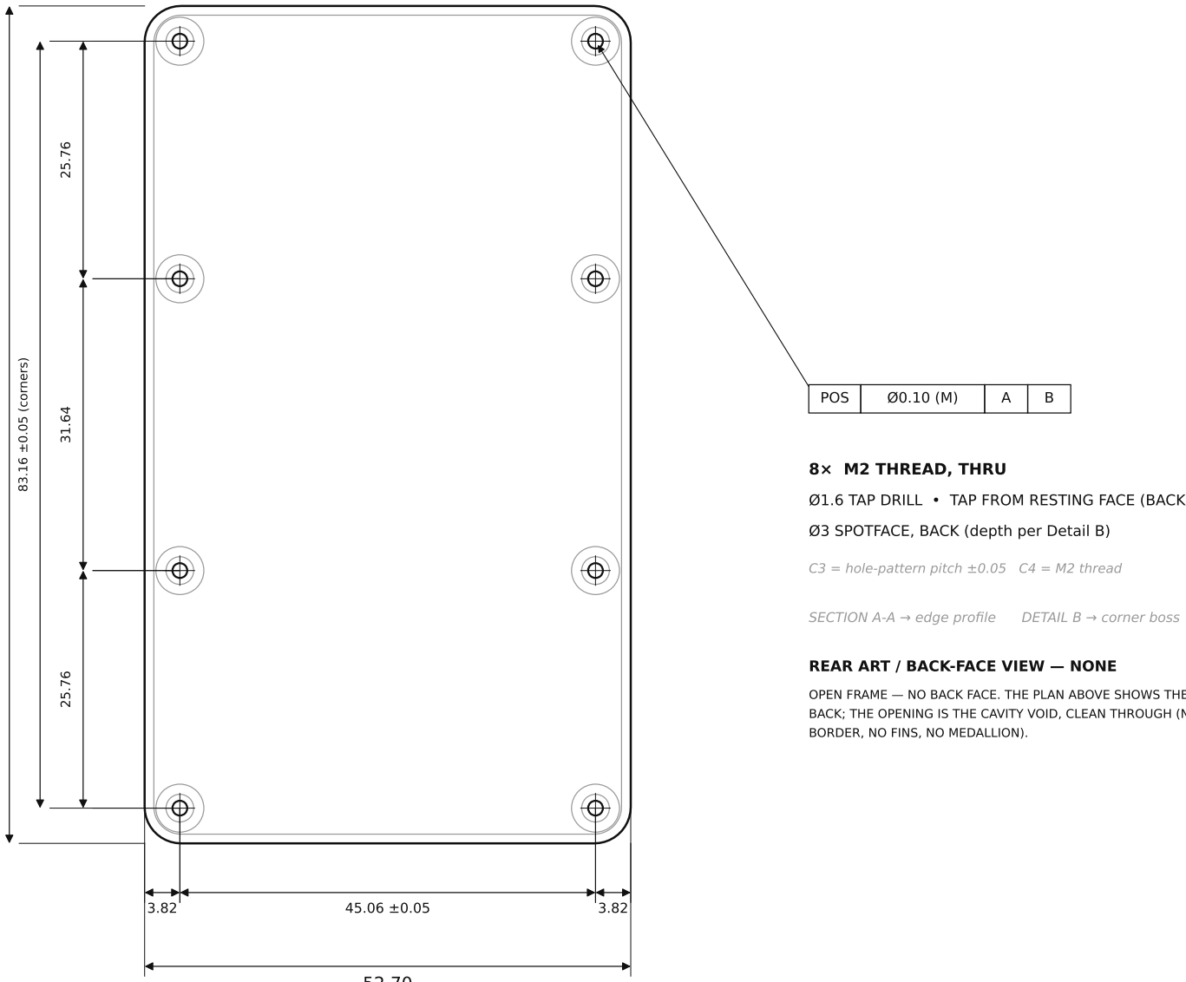
[picture p29: figure]
83.16 ±0.05 (corners); POS; 8× M2 THREAD, THRU; Ø3 SPOTFACE, BACK (depth per Detail B); SECTION A-A → edge profile; DETAIL B → corner boss; REAR ART / BACK-FACE VIEW — NONE; BORDER, NO FINS, NO MEDALLION).

52.70

90.80

## PLAN — FROM THE BACK (OPEN FRAME, NO BACK FACE) SCALE 1.5:1

### Ø1.6 TAP DRILL • TAP FROM RESTING FACE (BACK)

C3 = hole-pattern pitch ±0.05 C4 = M2 thread

OPEN FRAME — NO BACK FACE. THE PLAN ABOVE SHOWS THE FRAME FROM THE

BACK; THE OPENING IS THE CAVITY VOID, CLEAN THROUGH (NO FLOOR, NO

1.80

1.20 ±0.05

1.0

2.5 W-LIP (front; note 7)

0.10×45° RIM (top)

0.10×45° MOUTH

FLAT 0.05

0.10×45° LIP

0.10×45° RIM (btm) | open frame — no floor, no back face (note 6)
| PCB recess 0.60 (0.60 mm board)

## SECTION A-A (edge) SCALE 13:1

C1 = frame depth | C2 = PCB-rest-plane flatness | (open frame; PCB drops in from top)

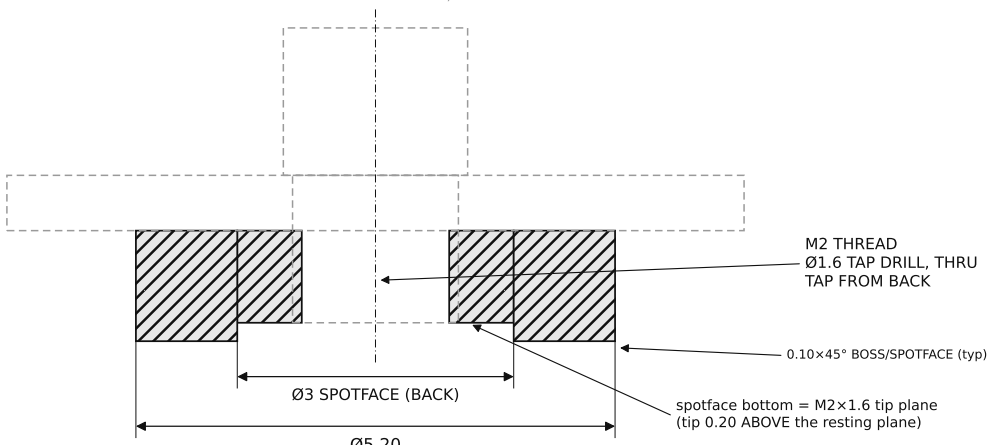
[picture p30: figure]
Ø3 SPOTFACE (BACK); M2 THREAD Ø1.6 TAP DRILL, THRU TAP FROM BACK; spotface bottom = M2×1.6 tip plane (tip 0.20 ABOVE the resting plane); 0.10×45° BOSS/SPOTFACE (typ)

Ø5.20

PCB + M2×1.6 BRASS SCREW — REF, NOT THIS PART

## DETAIL B (corner boss) 13:1

CRITICAL DIMENSIONS — C1 & C3 TOLERANCED ±0.05 (MARKED ON VIEWS); ALL OTHER FEATURES PER ISO 2768-1 (MEDIUM)

C1 | Frame depth (PCB-rest plane → resting plane; OPEN FRAME) | 1.20 ±0.05
C2 | PCB-rest plane flatness (lip + 8 bosses) | FLAT 0.05
C3 | 8× mounting holes (x 45.06; y rows 2.87/28.63/60.27/86.03) | ±0.05 (linear)
C4 | Mounting holes — tapped, thru, from back | M2 / Ø1.6 drill

### NOTES

1. MATERIAL: 316L STAINLESS (AUSTENITIC, MU_R~1.02 -- NOT CARBON/MARTENSITIC STEEL).
2. FINISH: BEAD-BLAST MATTE, ALL OVER. NO MARKING SERVICE — OPEN FRAME: NO BACK FACE, NO REAR ART.
3. GENERAL TOLERANCE PER ISO 2768-1 (MEDIUM). C1-C4 TOLERANCED AS LISTED; C1 & C3 = ±0.05. DATUMS: A = LEFT EDGE, B = BOTTOM EDGE, C = PCB-REST PLANE.
4. NO BRACE: AN OPEN FRAME HAS NO FLOOR TO RETAIN ONE (fit_rules.VARIANTS: brace_name=None). THE PCB REGISTERS IN THE 0.60 RECESS AND ON THE 8 BOSSES.
5. EDGE BREAKS - ALL 0.10x45°, FELT NOT SEEN, MODELED. CALLED OUT ON SEC A-A / DETAIL B: RIM = outer rim (top & bottom); MOUTH = recess mouth (around PCB); LIP = inner (cavity-side) lip edge; BOSS = boss + spotface bottom edges (Detail B). BREAK ALL OTHER EXPOSED EDGES 0.10x45°. CONCAVE JUNCTION CORNERS LEFT SHARP IN THE MODEL: FINISH WITH A Ø2.0 mm TOOL = R1.0 AS-MILLED. DEBURR 316L WITH SHARP TOOLS, SINGLE PASSES - AUSTENITIC STAINLESS WORK-HARDENS UNDER A RUBBING DEBURR.
6. NO FLOOR - OPEN FRAME. THE BACK OF EVERY B-SIDE COMPONENT FACES THE TABLE; THE FRAME'S RESTING PLANE (BOTTOM FACE) CARRIES THE ASSEMBLY.
DEPTH 1.20 = TALLEST B-SIDE PART 1.00 + 2×0.10 RESTING CLEARANCE (fit_rules.VARIANTS: resting-clearance-limited).
7. FRONT SUPPORT LIP IS ASYMMETRIC (SECTION A-A): WEST 2.5 / NORTH 2.0 / SOUTH 2.0 FOR PCB RIGIDITY; EAST 1.0 CLEARING THE JP1/TP1 PADS, THE NFC COIL (A GROUNDED LIP WOULD DETUNE IT), AND C7 (x49.55, THE ONE EAST-EDGE PART LEFT AFTER v4 REMOVED THE Q1/U4/R7/R9 CLAMP CLUSTER + D9/D10/D11); WIDENING TO 2.5 ONLY AT THE SOUTH END (y0-10, CLEAR OF ALL). NO EXTERIOR BACK BORDER — THE OPEN FRAME HAS NO BACK FACE.
8. NO INTERNAL RIBS, SUPPORT POSTS, OR BRACE: OPEN FRAME. THE BOARD SPANS FREE BETWEEN THE LIP AND THE 8 BOSSES — HANDLE THE ASSEMBLY ACCORDINGLY.
9. PCB RECESS = 0.60 DEEP (RECEIVES THE 0.60 mm BOARD; SLIP FIT, NOT A PRESS FIT). 3D STEP GOVERNS ALL GEOMETRY; STL NOT FOR CNC.
10. PART = OPEN FRAME ONLY. PCB, AND 8× M2×1.6 BRASS SLOTTED-CHEESE SCREWS (HEAD Ø3.8) SUPPLIED SEPARATELY.

### SOLAR-GLOW DRH — AIR OPEN FRAME (316L, NO BACK FACE)

DWG solar-glow-drh-frame-air-316L | REV air
MATERIAL 316L stainless | FINISH BEAD-BLAST MATTE
UNITS mm | SCALE AS NOTED
BBOX 52.70 x 90.80 x 1.80 3rd-angle | SHEET 1/1

GENERAL TOLERANCES (UNLESS OTHERWISE NOTED, mm)

LINEAR & HOLE-POSITION DIMS | ISO 2768-m
FRAME DEPTH C1 (SECTION A-A) | 1.20 ±0.05
HOLE-PATTERN PITCH C3 (8 HOLES) | x 45.06 / y 25.76-31.64-25.76 ±0.05
PCB-REST FLATNESS C2 | FLAT 0.05
