devinhorowitz/solar-business-card/docs/PredictableDesigns_DesignReviewChecklist_Enclosure.pdf

# MechanicalEnclosureDesign

# DesignReview Checklist

Copyright2025PredictableDesignsLLC

## 1.1.Mechanicalresistance

## 1MECHANICAL

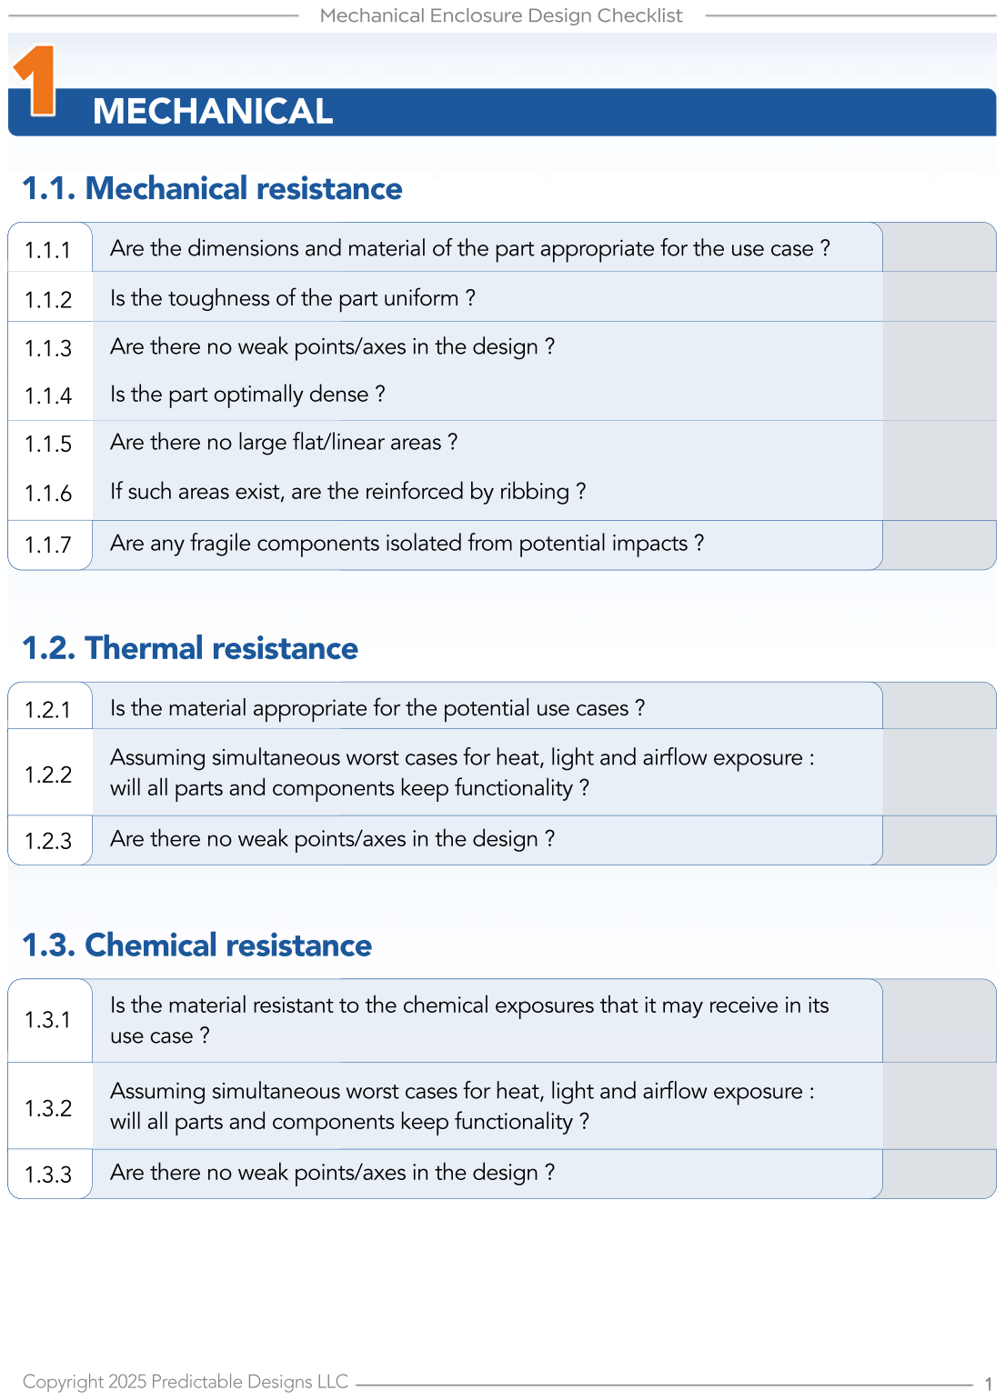
[picture p38: page 2]

1.3.1 Isthematerialresistanttothechemicalexposuresthatitmayreceiveinits usecase?

1.3.2

Assumingsimultaneousworstcasesforheat,lightandairflowexposure: willallpartsandcomponentskeepfunctionality?

1.3.3 Aretherenoweakpoints/axesinthedesign?

## 1.3.Chemicalresistance

1.3.1 Isthematerialresistanttothechemicalexposuresthatitmayreceiveinits

## 1.2.Thermalresistance

1.2.1 Isthematerialappropriateforthepotentialusecases?

1.2.2

Assumingsimultaneousworstcasesforheat,lightandairflowexposure: willallpartsandcomponentskeepfunctionality?

1.2.3 Aretherenoweakpoints/axesinthedesign?

1.1.1 Arethedimensionsandmaterialofthepartappropriatefortheusecase?

1.1.2 Isthetoughnessofthepartuniform?

1.1.3 Aretherenoweakpoints/axesinthedesign?
1.1.4 Isthepartoptimallydense?
1.1.5 Aretherenolargeflat/linearareas?

1.1.6 Ifsuchareasexist,arethereinforcedbyribbing?

1.1.7 Areanyfragilecomponentsisolatedfrompotentialimpacts?

Copyright2025PredictableDesignsLLC | 1

MechanicalEnclosureDesignChecklist

## 1.4.Thermalresistance

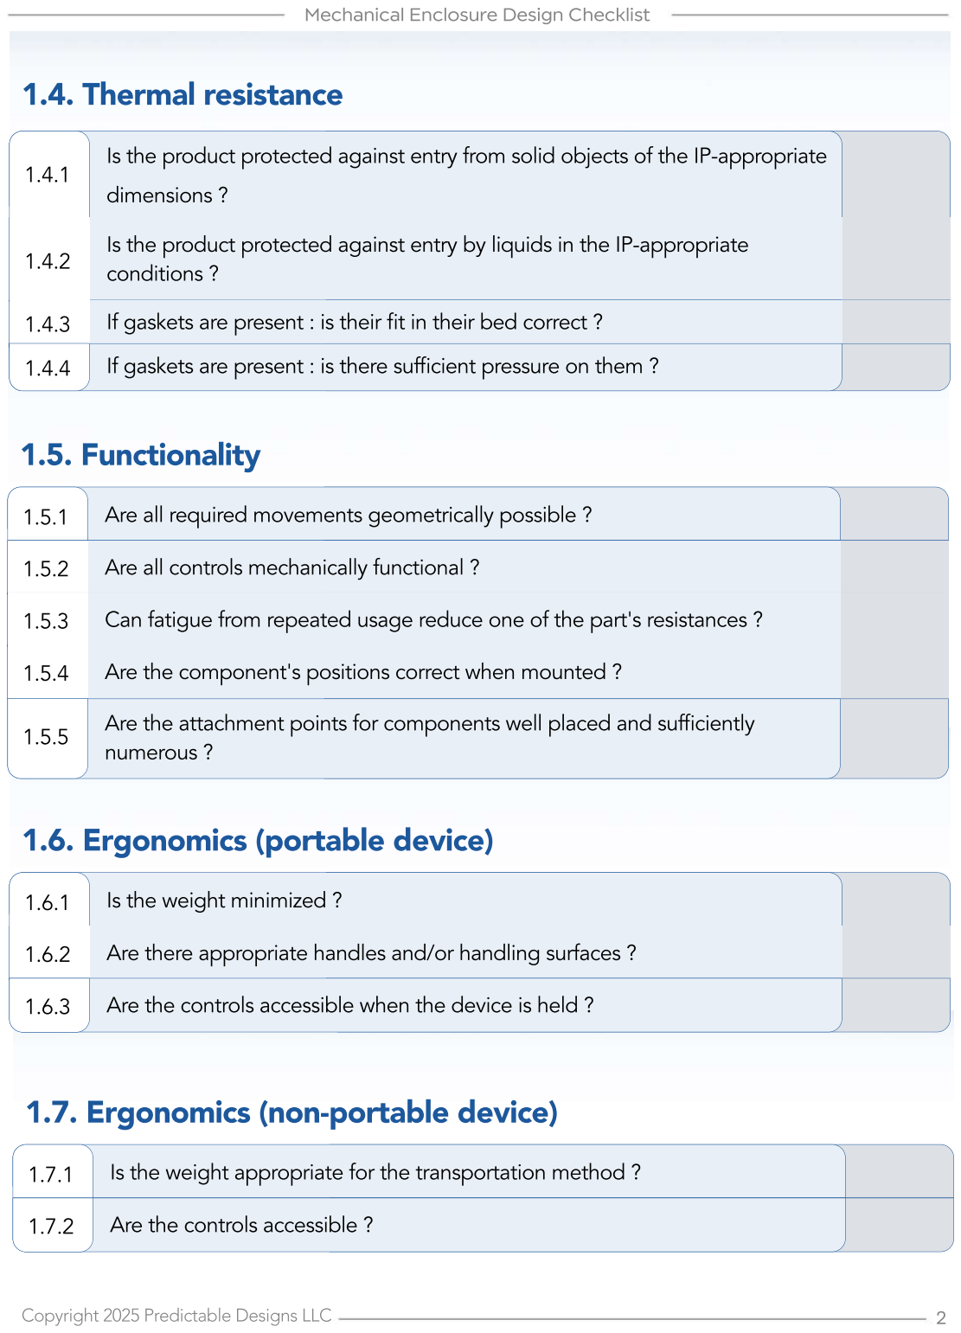
[picture p39: page 3]

## 1.7.Ergonomics(non-portabledevice)

1.7.1 Istheweightappropriateforthetransportationmethod?

1.7.2 Arethecontrolsaccessible?

1.6.1 Istheweightminimized?

1.6.2 Arethereappropriatehandlesand/orhandlingsurfaces?

1.6.3 Arethecontrolsaccessiblewhenthedeviceisheld?

## 1.6.Ergonomics(portabledevice)

1.5.1 Areallrequiredmovementsgeometricallypossible?

1.5.2 Areallcontrolsmechanicallyfunctional?

1.5.3 Canfatiguefromrepeatedusagereduceoneofthepart'sresistances?

1.5.4 Arethecomponent'spositionscorrectwhenmounted?

1.5.5 Aretheattachmentpointsforcomponentswellplacedandsufficiently numerous?

## 1.5.Functionality

1.5.1 Areallrequiredmovementsgeometricallypossible?

1.4.1

IstheproductprotectedagainstentryfromsolidobjectsoftheIP-appropriate dimensions?

1.4.2

IstheproductprotectedagainstentrybyliquidsintheIP-appropriate conditions?

1.4.3 Ifgasketsarepresent:istheirfitintheirbedcorrect? 1.4.4 Ifgasketsarepresent:istheresufficientpressureonthem?

## 1.8.Maintenance

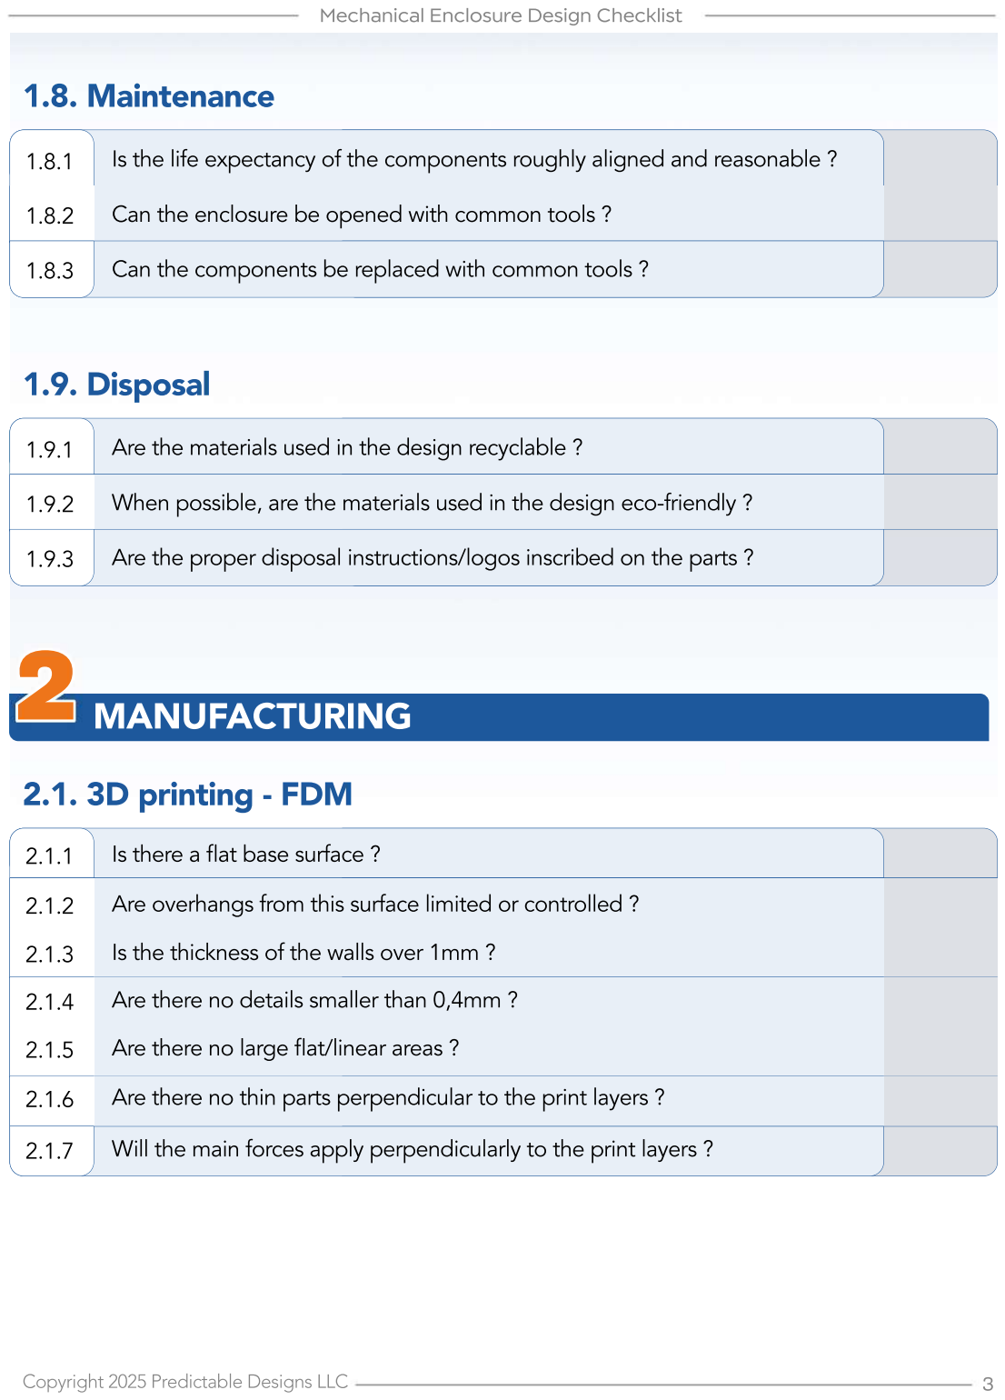
[picture p40: page 4]

2.1.1 Isthereaflatbasesurface?

2.1.2 Areoverhangsfromthissurfacelimitedorcontrolled?

2.1.3 Isthethicknessofthewallsover1mm?
2.1.4 Aretherenodetailssmallerthan0,4mm?
2.1.5 Aretherenolargeflat/linearareas?

2.1.6 Aretherenothinpartsperpendiculartotheprintlayers?

2.1.7 Willthemainforcesapplyperpendicularlytotheprintlayers?

## 2.1.3Dprinting-FDM

## 2MANUFACTURING

1.9.3 Aretheproperdisposalinstructions/logosinscribedontheparts?

## 1.9.Disposal

1.9.1 Arethematerialsusedinthedesignrecyclable?

1.9.2 Whenpossible,arethematerialsusedinthedesigneco-friendly?

1.8.1 Isthelifeexpectancyofthecomponentsroughlyalignedandreasonable?

1.8.2 Cantheenclosurebeopenedwithcommontools?

1.8.3 Canthecomponentsbereplacedwithcommontools?

## 2.2.3Dprinting-SLAandDLP

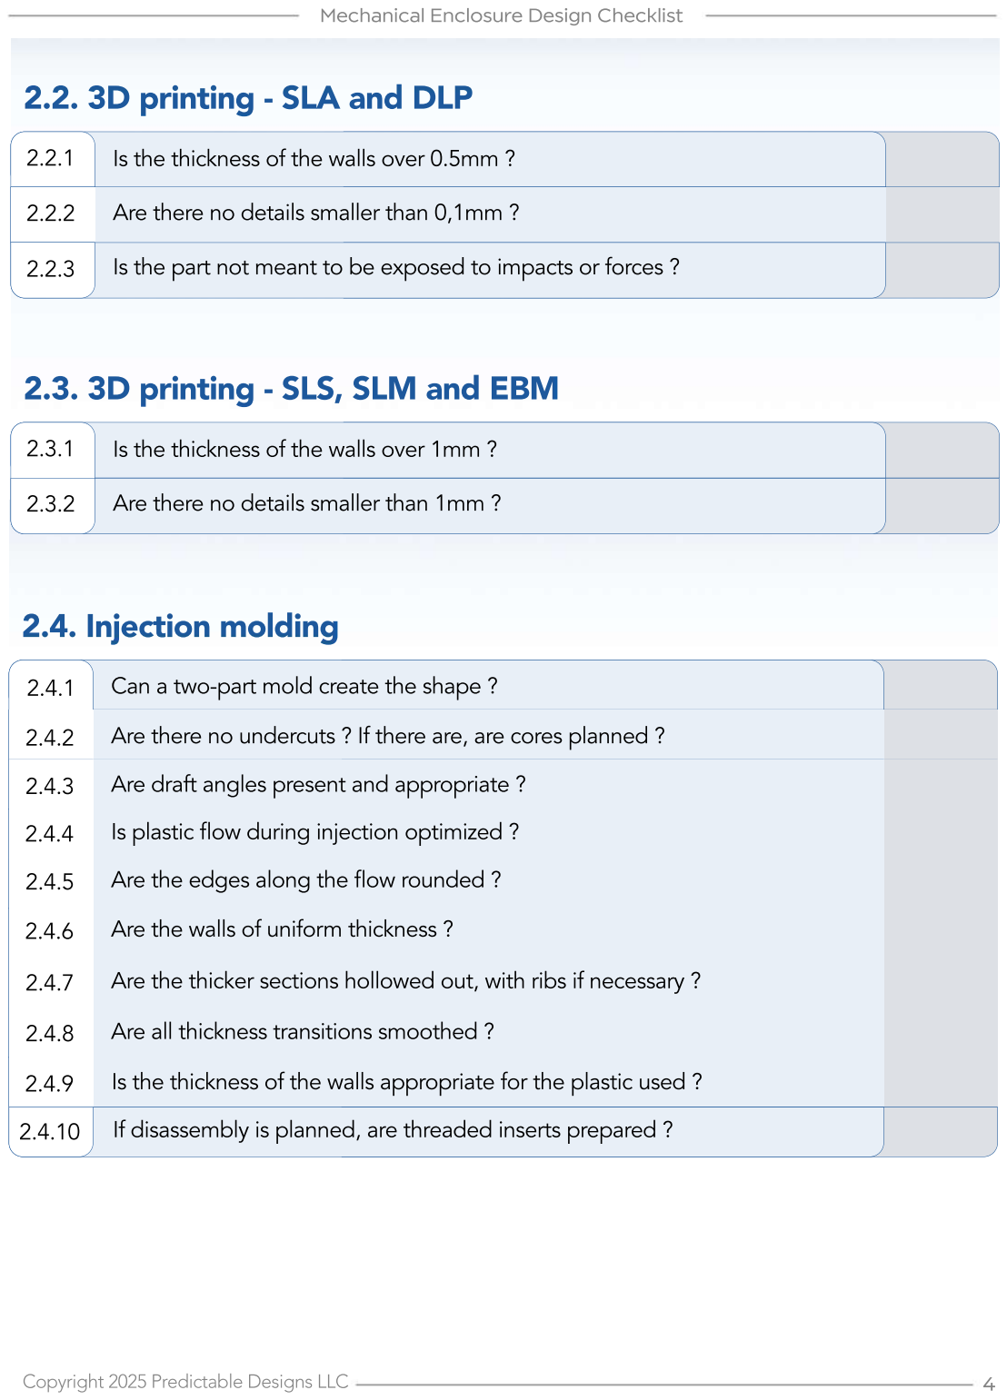
[picture p41: page 5]

2.4.4 Isplasticflowduringinjectionoptimized? 2.4.5 Aretheedgesalongtheflowrounded?

2.4.6 Arethewallsofuniformthickness?

2.4.7 Arethethickersectionshollowedout,withribsifnecessary?

2.4.8 Areallthicknesstransitionssmoothed?

2.4.9 Isthethicknessofthewallsappropriatefortheplasticused? 2.4.10 Ifdisassemblyisplanned,arethreadedinsertsprepared?

## 2.4.Injectionmolding

2.4.1 Canatwo-partmoldcreatetheshape?

2.4.2 Aretherenoundercuts?Ifthereare,arecoresplanned?

2.4.3 Aredraftanglespresentandappropriate?

## 2.3.3Dprinting-SLS,SLM andEBM

2.3.1 Isthethicknessofthewallsover1mm?

2.3.2 Aretherenodetailssmallerthan1mm?

2.2.1 Isthethicknessofthewallsover0.5mm?

2.2.2 Aretherenodetailssmallerthan0,1mm?

2.2.3 Isthepartnotmeanttobeexposedtoimpactsorforces?

## 2.5.Machining

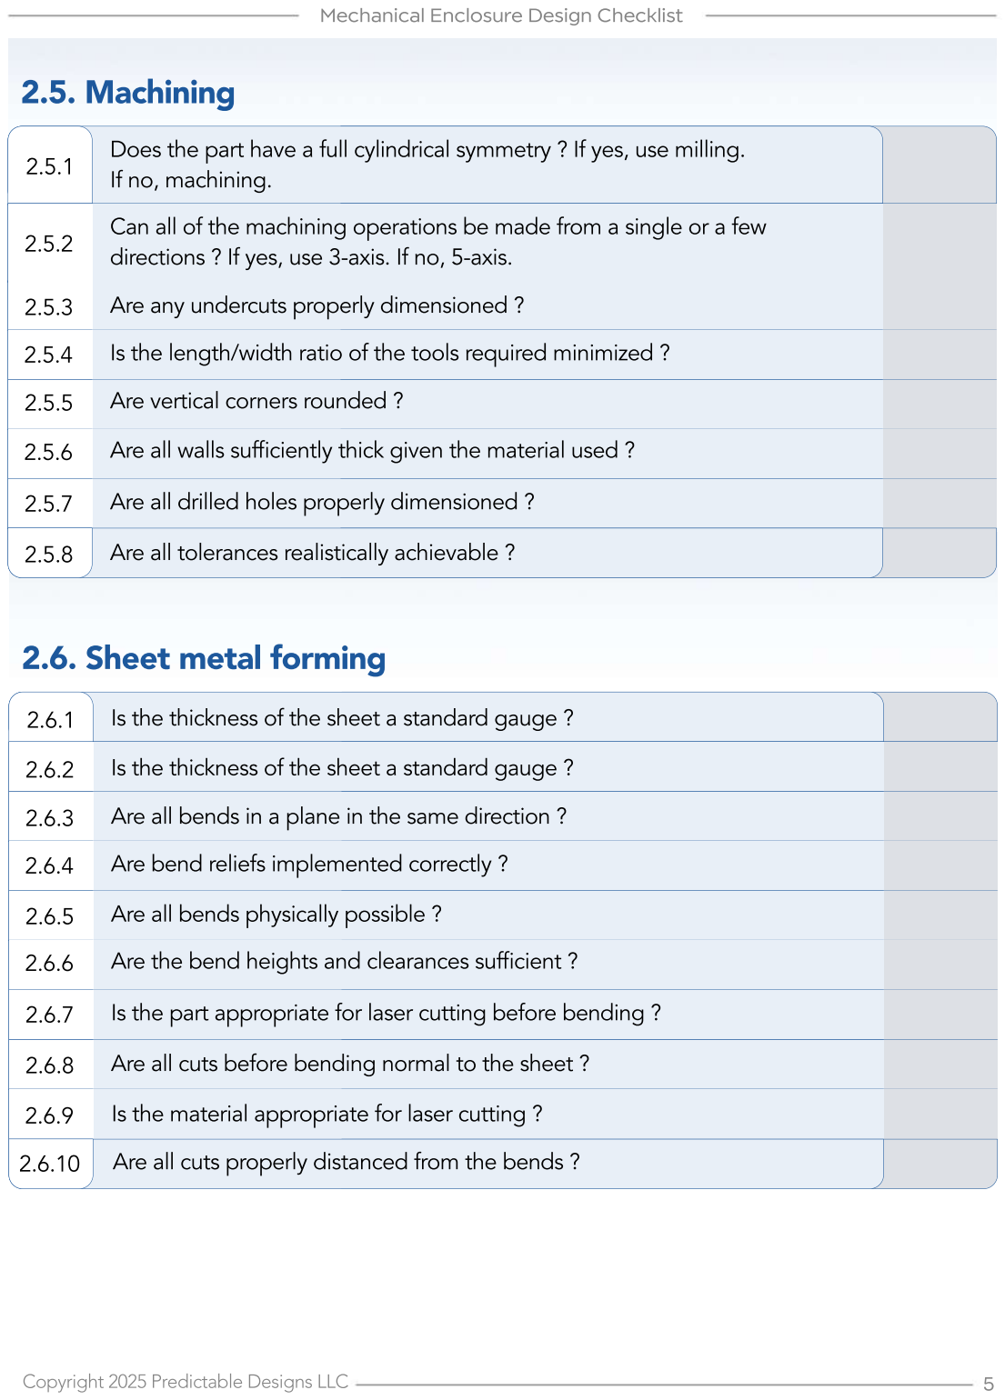
[picture p42: page 6]

## 2.6.Sheetmetalforming

2.6.1 Isthethicknessofthesheetastandardgauge?

2.6.2 Isthethicknessofthesheetastandardgauge?

2.6.3 Areallbendsinaplaneinthesamedirection? 2.6.4 Arebendreliefsimplementedcorrectly?

2.6.5 Areallbendsphysicallypossible?
2.6.6 Arethebendheightsandclearancessufficient?

2.6.7 Isthepartappropriateforlasercuttingbeforebending?

2.6.8 Areallcutsbeforebendingnormaltothesheet?

2.6.9 Isthematerialappropriateforlasercutting?
2.6.10 Areallcutsproperlydistancedfromthebends?

2.5.1

Doestheparthaveafullcylindricalsymmetry?Ifyes,usemilling. Ifno,machining.

2.5.2

Canallofthemachiningoperationsbemadefromasingleorafew directions?Ifyes,use3-axis.Ifno,5-axis.
2.5.3 Areanyundercutsproperlydimensioned?
2.5.4 Isthelength/widthratioofthetoolsrequiredminimized? 2.5.5 Areverticalcornersrounded?

2.5.6 Areallwallssufficientlythickgiventhematerialused?

2.5.7 Arealldrilledholesproperlydimensioned?

2.5.8 Arealltolerancesrealisticallyachievable?

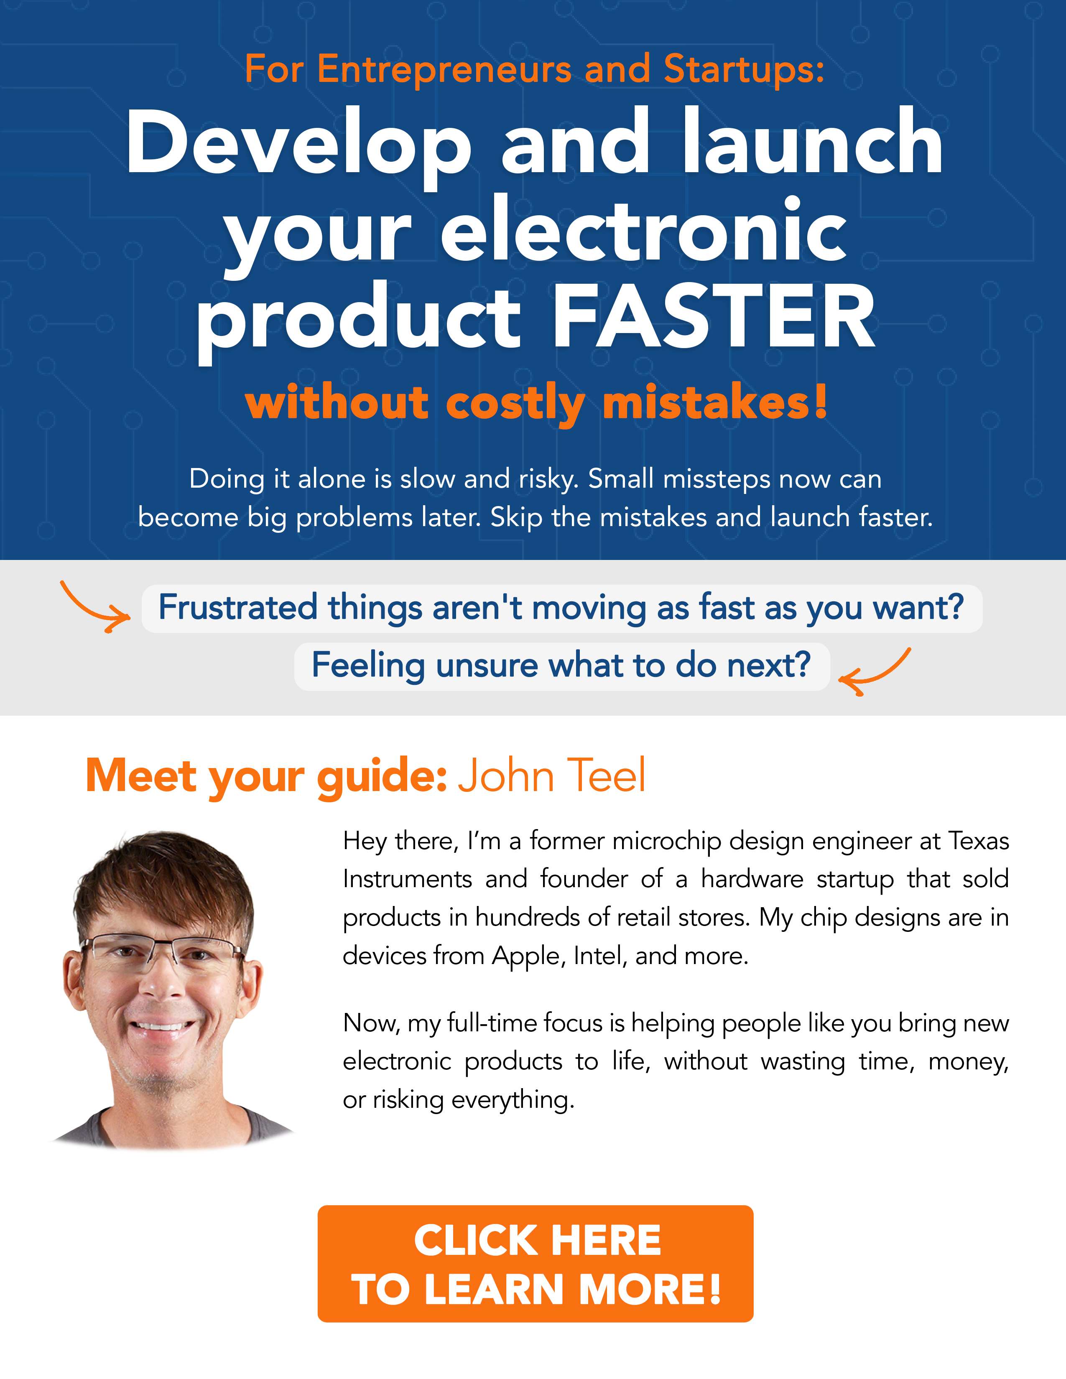
[picture p43: page 7]
