devinhorowitz/solar-business-card/enclosure/brace/solar-glow-drh-diffuser-brace-DRAWING.png

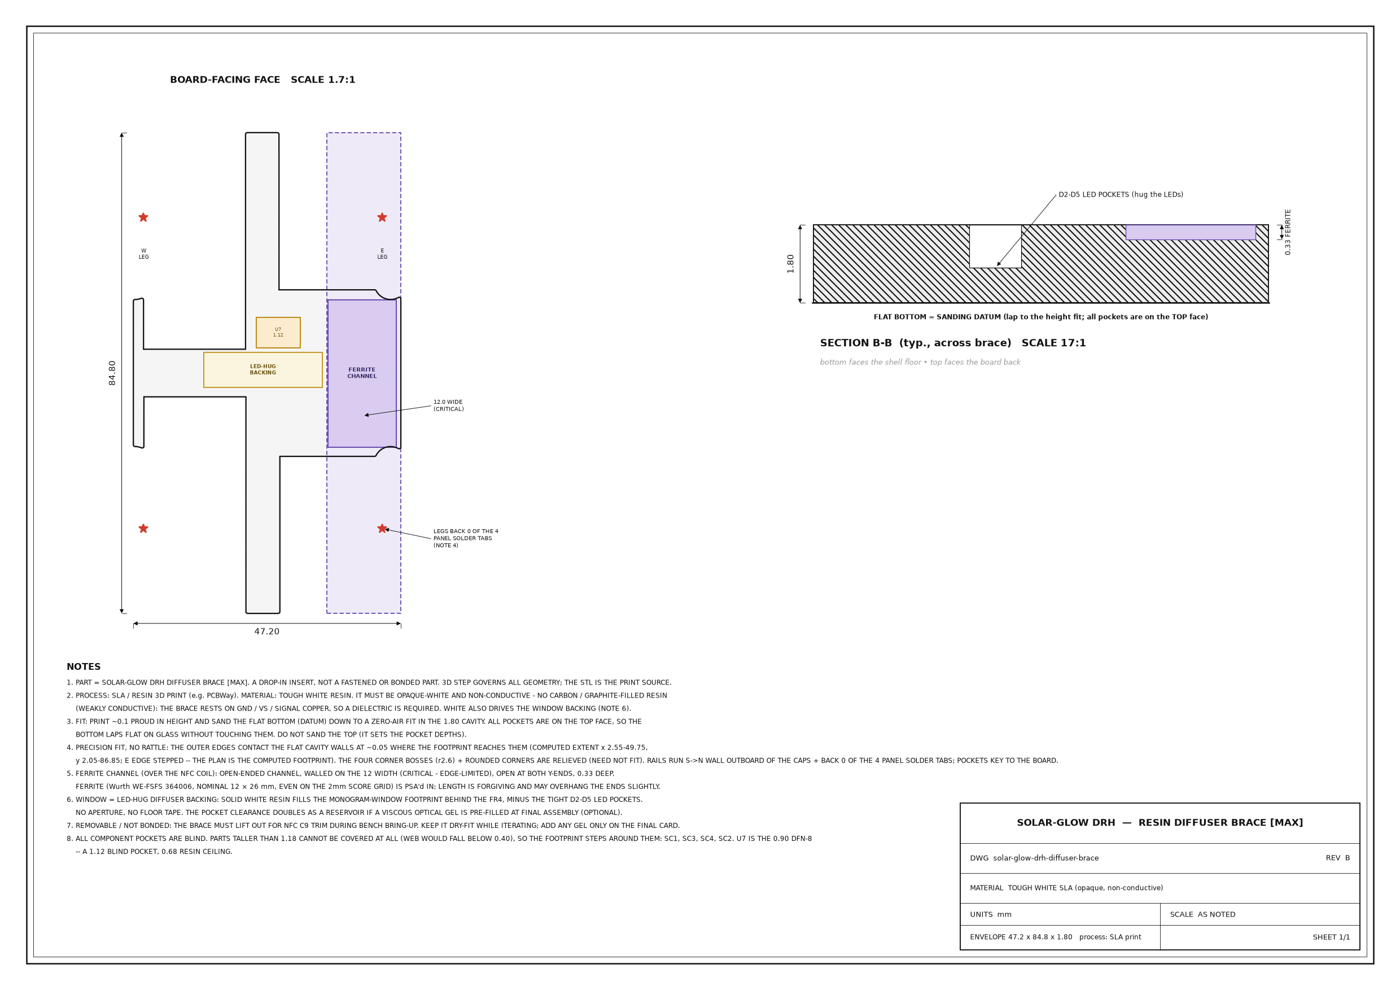
enclosure/brace/solar-glow-drh-diffuser-brace-DRAWING.png
