devinhorowitz/solar-business-card/enclosure/brace/solar-glow-drh-diffuser-brace-lite-pocket-map.png

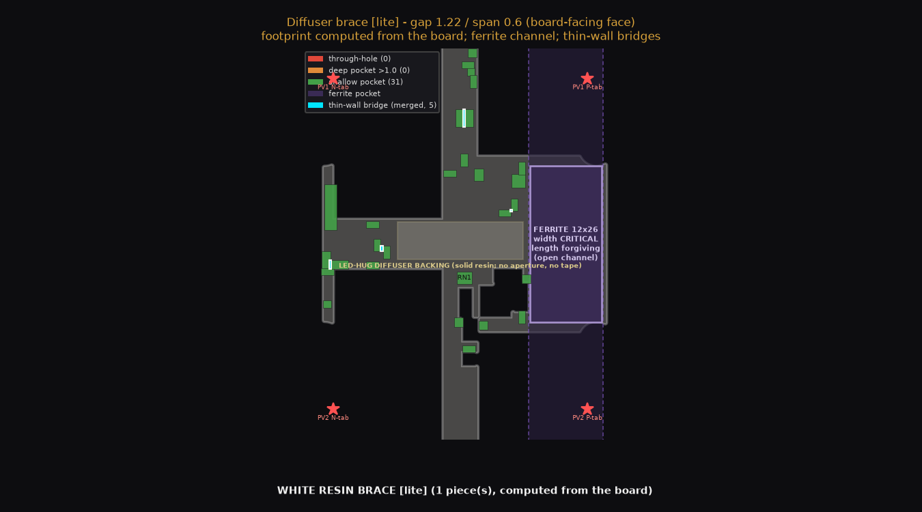
enclosure/brace/solar-glow-drh-diffuser-brace-lite-pocket-map.png
