devinhorowitz/solar-business-card/enclosure/solar-glow-drh-frame-air-316L-DRAWING.png

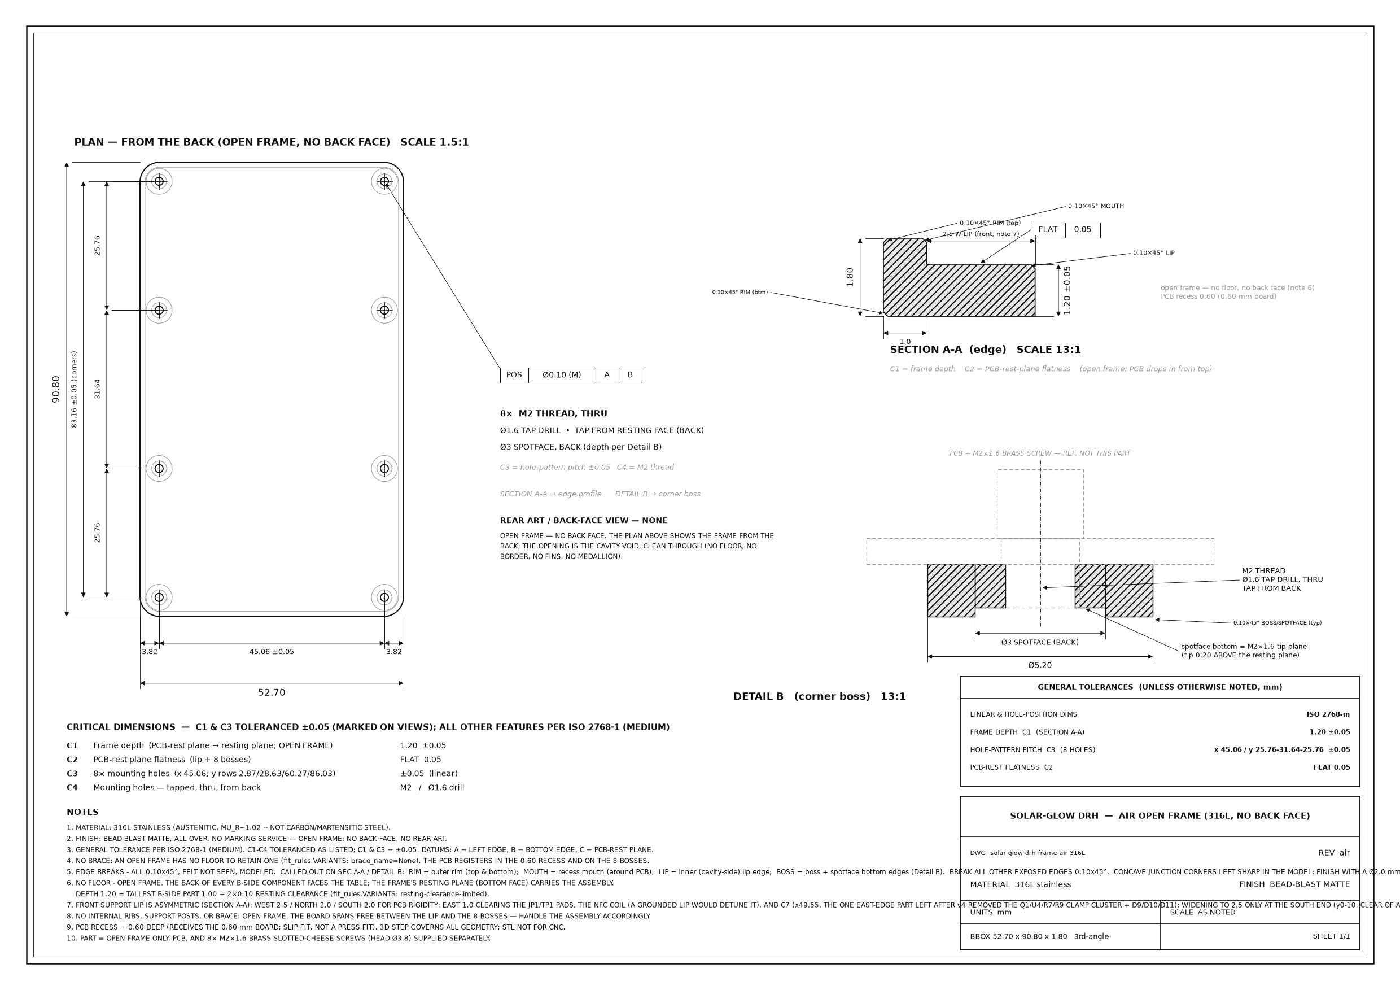
enclosure/solar-glow-drh-frame-air-316L-DRAWING.png
