devinhorowitz/solar-business-card/enclosure/solar-glow-drh-shell-lite-Ti-DRAWING.png

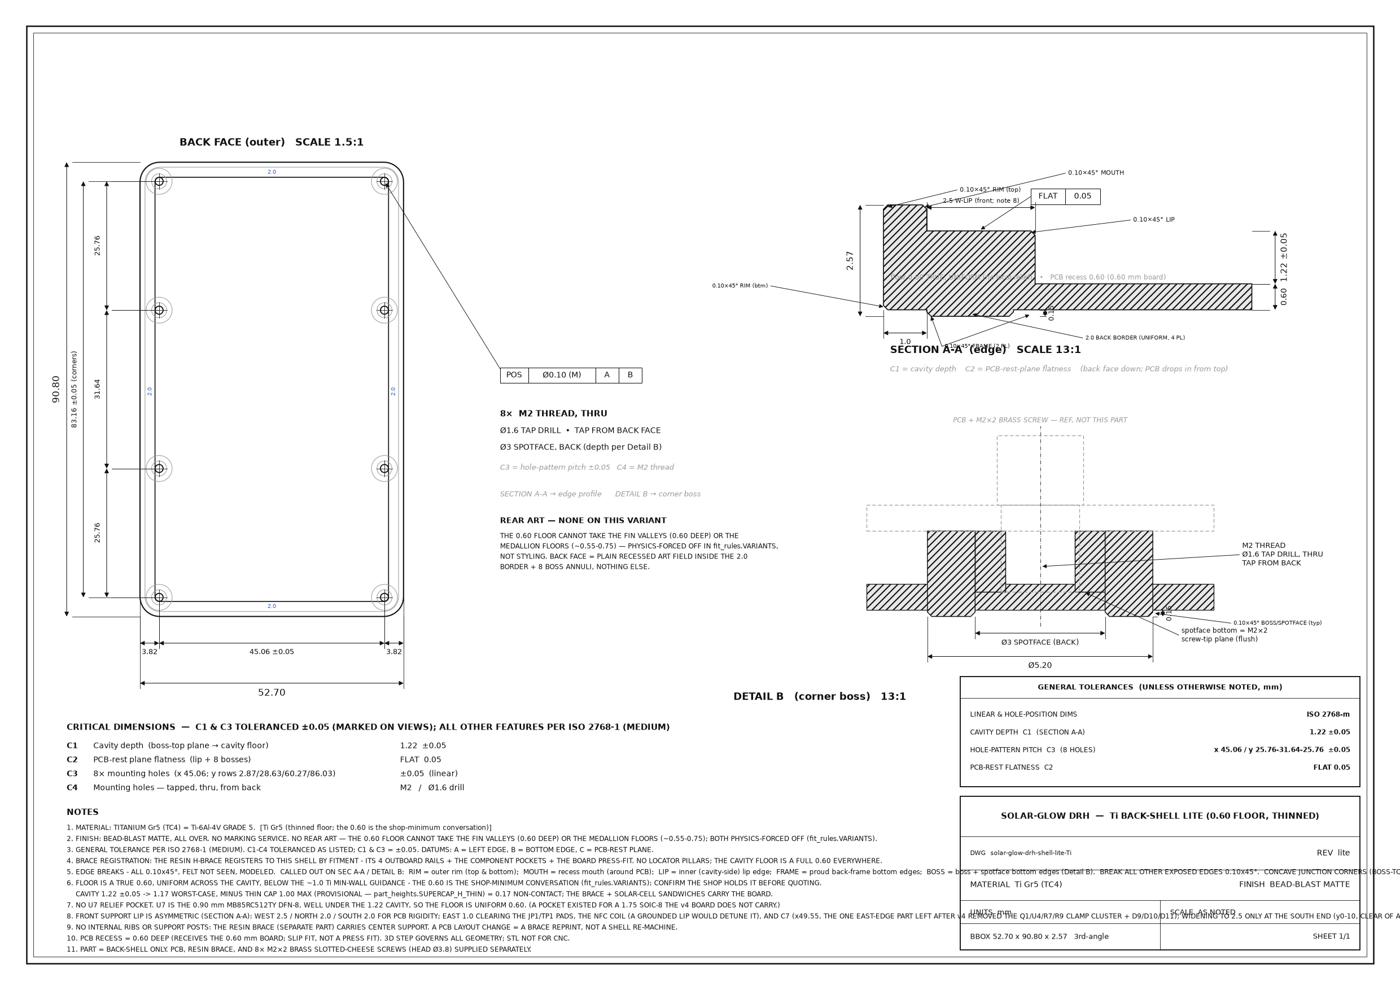
enclosure/solar-glow-drh-shell-lite-Ti-DRAWING.png
