devinhorowitz/solar-business-card/enclosure/solar-glow-drh-v4_0-backshell-0p6b-brace-DRAWING.png

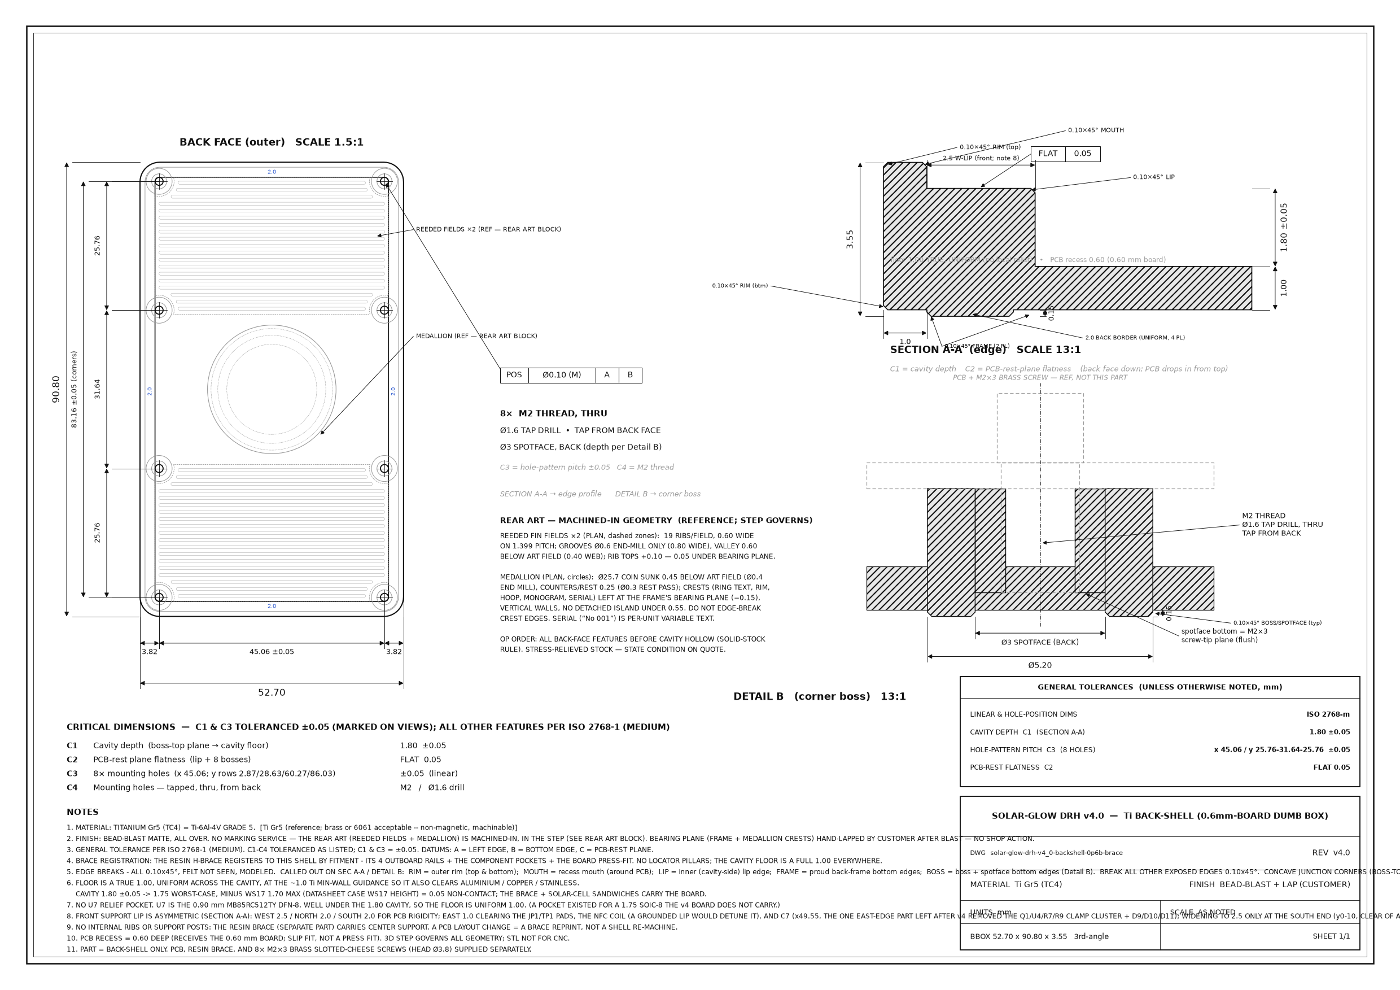
enclosure/solar-glow-drh-v4_0-backshell-0p6b-brace-DRAWING.png
