devinhorowitz/solar-business-card/Generated/docs/solar-glow-drh-v4_0-bottom.png

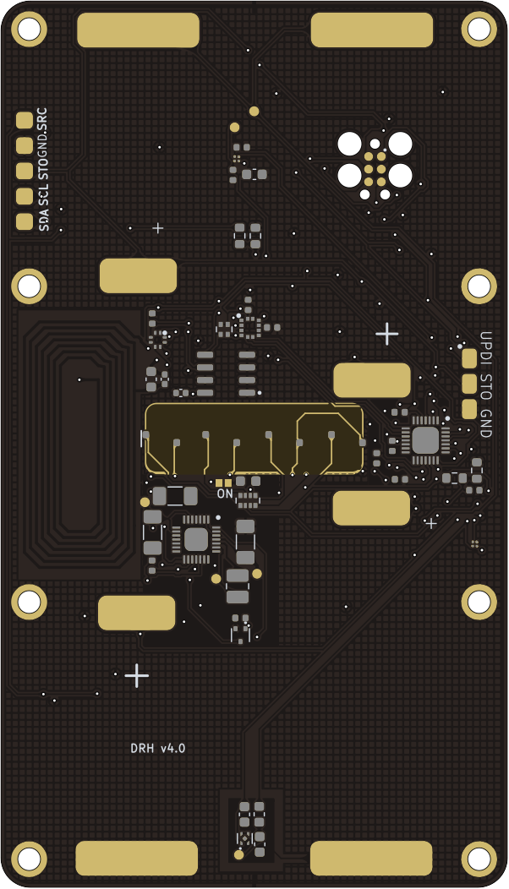
Generated/docs/solar-glow-drh-v4_0-bottom.png
