devinhorowitz/solar-business-card/Generated/docs/solar-glow-drh-v4_0-card-face.png

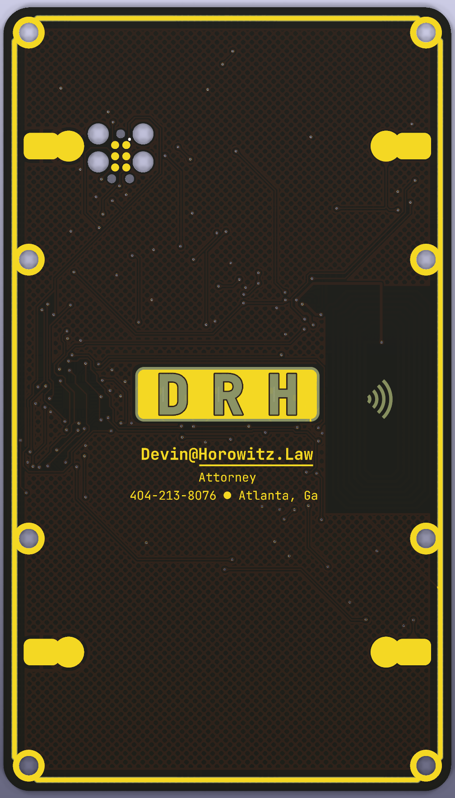
Generated/docs/solar-glow-drh-v4_0-card-face.png
