devinhorowitz/solar-business-card/Generated/docs/solar-glow-drh-v4_0-card-grazing.png

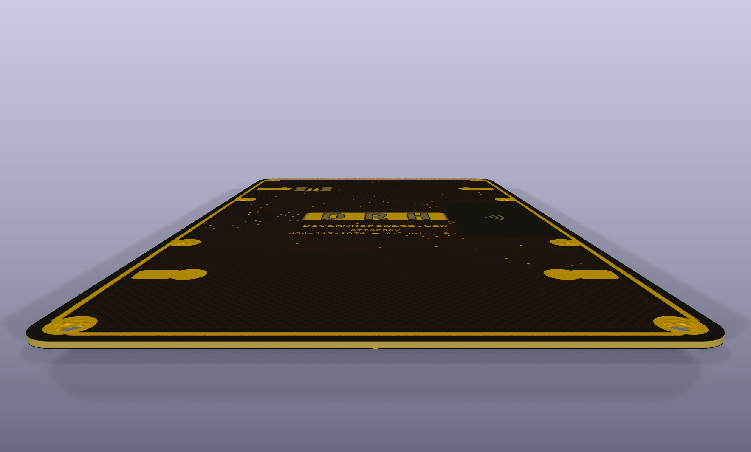
Generated/docs/solar-glow-drh-v4_0-card-grazing.png
