devinhorowitz/solar-business-card/Generated/docs/solar-glow-drh-v4_0-panel-angle.png

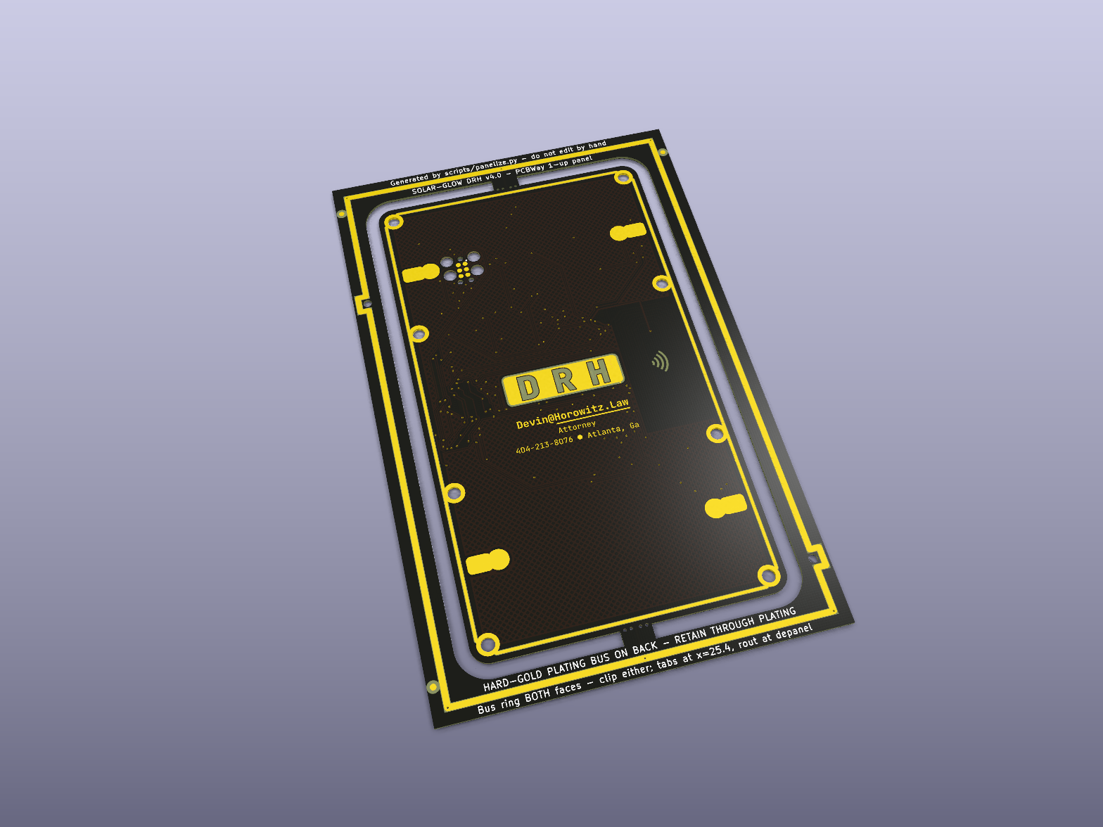
Generated/docs/solar-glow-drh-v4_0-panel-angle.png
