devinhorowitz/solar-business-card/enclosure/brace/solar-glow-drh-diffuser-brace-DRAWING.pdf

## BOARD-FACING FACE SCALE 1.7:1

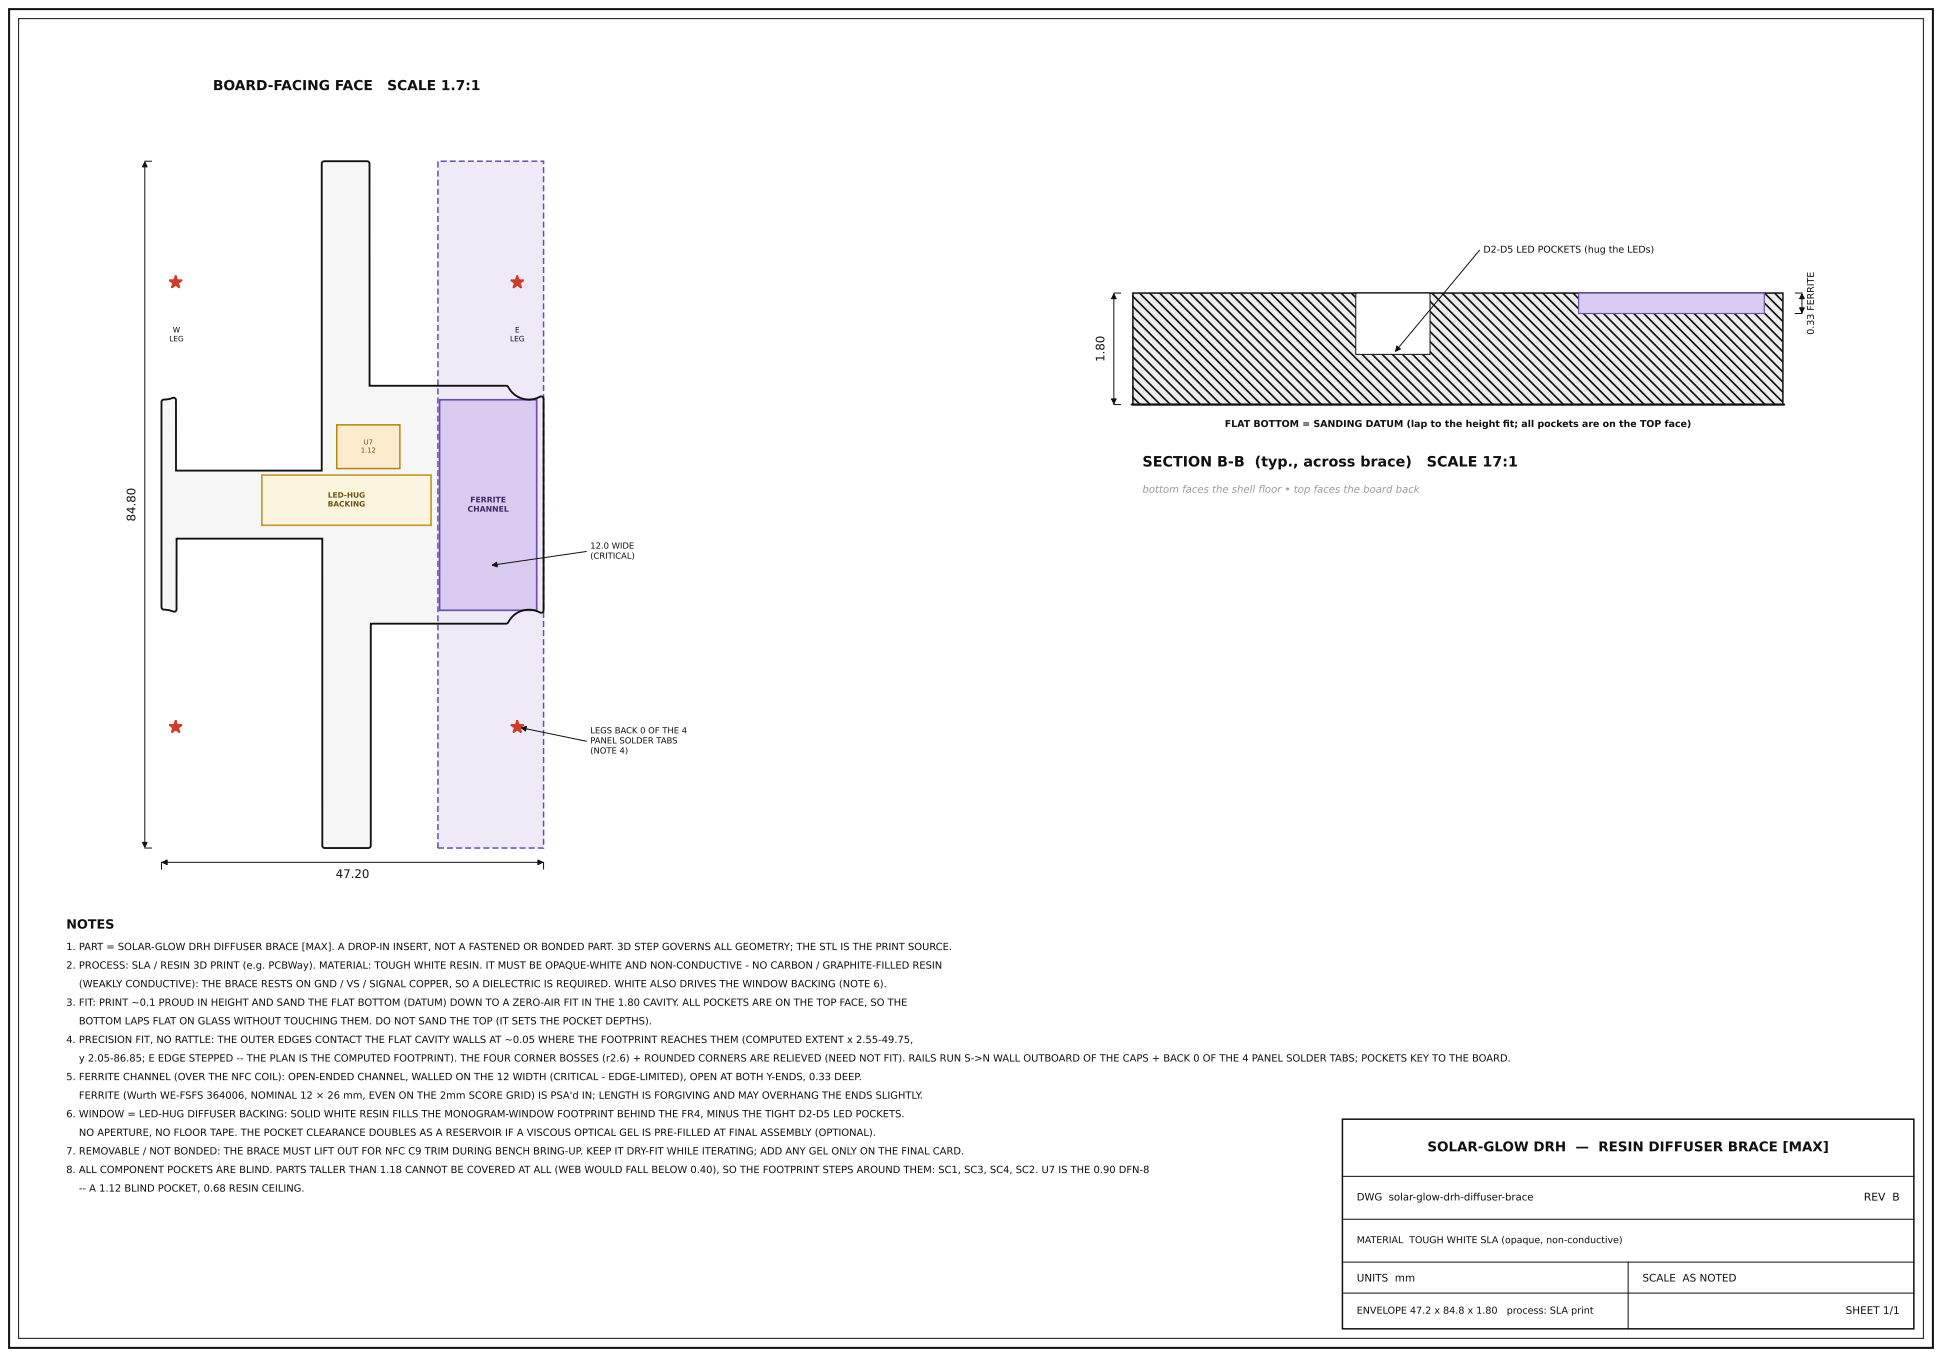
[picture p66: page 1]
FERRITE CHANNEL; LED-HUG BACKING; W LEG; E LEG; 12.0 WIDE (CRITICAL); 0.33 FERRITE; NOTES; DWG solar-glow-drh-diffuser-brace; REV B

D2-D5 LED POCKETS (hug the LEDs)

FLAT BOTTOM = SANDING DATUM (lap to the height fit; all pockets are on the TOP face)

SECTION B-B (typ., across brace) SCALE 17:1
bottom faces the shell floor • top faces the board back

LEGS BACK 0 OF THE 4
PANEL SOLDER TABS
(NOTE 4)

1. PART = SOLAR-GLOW DRH DIFFUSER BRACE [MAX]. A DROP-IN INSERT, NOT A FASTENED OR BONDED PART. 3D STEP GOVERNS ALL GEOMETRY; THE STL IS THE PRINT SOURCE.

2. PROCESS: SLA / RESIN 3D PRINT (e.g. PCBWay). MATERIAL: TOUGH WHITE RESIN. IT MUST BE OPAQUE-WHITE AND NON-CONDUCTIVE - NO CARBON / GRAPHITE-FILLED RESIN

(WEAKLY CONDUCTIVE): THE BRACE RESTS ON GND / VS / SIGNAL COPPER, SO A DIELECTRIC IS REQUIRED. WHITE ALSO DRIVES THE WINDOW BACKING (NOTE 6).

3. FIT: PRINT ~0.1 PROUD IN HEIGHT AND SAND THE FLAT BOTTOM (DATUM) DOWN TO A ZERO-AIR FIT IN THE 1.80 CAVITY. ALL POCKETS ARE ON THE TOP FACE, SO THE

BOTTOM LAPS FLAT ON GLASS WITHOUT TOUCHING THEM. DO NOT SAND THE TOP (IT SETS THE POCKET DEPTHS).

4. PRECISION FIT, NO RATTLE: THE OUTER EDGES CONTACT THE FLAT CAVITY WALLS AT ~0.05 WHERE THE FOOTPRINT REACHES THEM (COMPUTED EXTENT x 2.55-49.75,

y 2.05-86.85; E EDGE STEPPED -- THE PLAN IS THE COMPUTED FOOTPRINT). THE FOUR CORNER BOSSES (r2.6) + ROUNDED CORNERS ARE RELIEVED (NEED NOT FIT). RAILS RUN S->N WALL OUTBOARD OF THE CAPS + BACK 0 OF THE 4 PANEL SOLDER TABS; POCKETS KEY TO THE BOARD.

5. FERRITE CHANNEL (OVER THE NFC COIL): OPEN-ENDED CHANNEL, WALLED ON THE 12 WIDTH (CRITICAL - EDGE-LIMITED), OPEN AT BOTH Y-ENDS, 0.33 DEEP.

FERRITE (Wurth WE-FSFS 364006, NOMINAL 12 × 26 mm, EVEN ON THE 2mm SCORE GRID) IS PSA'd IN; LENGTH IS FORGIVING AND MAY OVERHANG THE ENDS SLIGHTLY.

6. WINDOW = LED-HUG DIFFUSER BACKING: SOLID WHITE RESIN FILLS THE MONOGRAM-WINDOW FOOTPRINT BEHIND THE FR4, MINUS THE TIGHT D2-D5 LED POCKETS.

NO APERTURE, NO FLOOR TAPE. THE POCKET CLEARANCE DOUBLES AS A RESERVOIR IF A VISCOUS OPTICAL GEL IS PRE-FILLED AT FINAL ASSEMBLY (OPTIONAL).

7. REMOVABLE / NOT BONDED: THE BRACE MUST LIFT OUT FOR NFC C9 TRIM DURING BENCH BRING-UP. KEEP IT DRY-FIT WHILE ITERATING; ADD ANY GEL ONLY ON THE FINAL CARD.

SOLAR-GLOW DRH — RESIN DIFFUSER BRACE [MAX]

8. ALL COMPONENT POCKETS ARE BLIND. PARTS TALLER THAN 1.18 CANNOT BE COVERED AT ALL (WEB WOULD FALL BELOW 0.40), SO THE FOOTPRINT STEPS AROUND THEM: SC1, SC3, SC4, SC2. U7 IS THE 0.90 DFN-8

-- A 1.12 BLIND POCKET, 0.68 RESIN CEILING.

MATERIAL TOUGH WHITE SLA (opaque, non-conductive)

UNITS mm | SCALE AS NOTED

ENVELOPE 47.2 x 84.8 x 1.80 process: SLA print | SHEET 1/1
