devinhorowitz/solar-business-card/Generated/gerbers/solar-glow-drh-v4_0-NPTH_drill_map.pdf

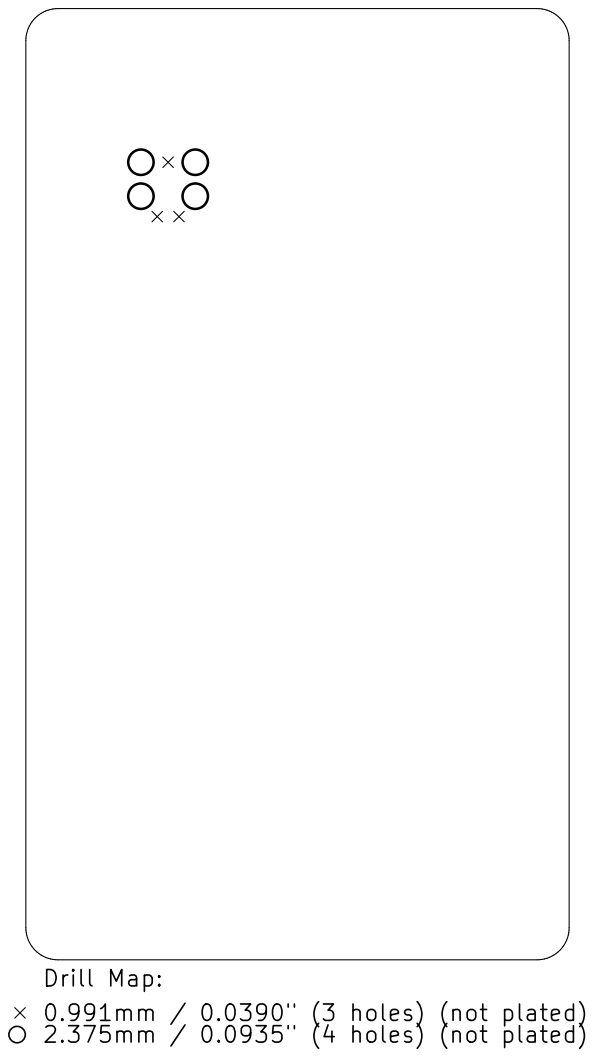
[picture p67: page 1]

Drill Map:
0.991mm / 0.0390" (3 holes) (not plated) 2.375mm / 0.0935" (4 holes) (not plated)
