devinhorowitz/solar-business-card/Generated/panel/gerbers/solar-glow-drh-v4_0-panel-NPTH_drill_map.pdf

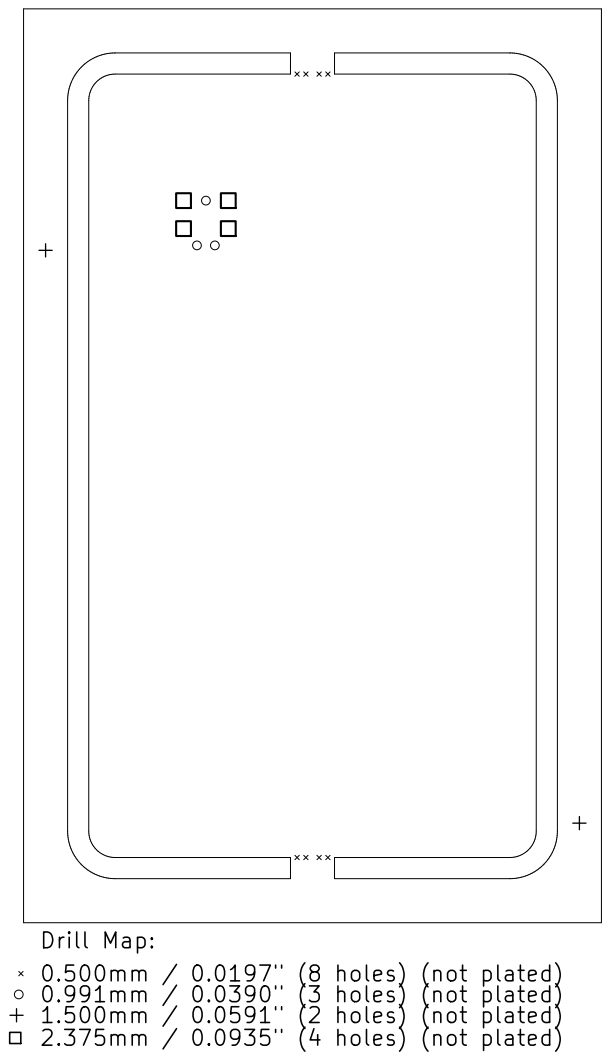
[picture p68: page 1]

Drill Map:
0.500mm / 0.0197" (8 holes) (not plated) 0.991mm / 0.0390" (3 holes) (not plated) 1.500mm / 0.0591" (2 holes) (not plated) 2.375mm / 0.0935" (4 holes) (not plated)
