devinhorowitz/solar-business-card/Generated/gerbers/solar-glow-drh-v4_0-PTH_drill_map.pdf

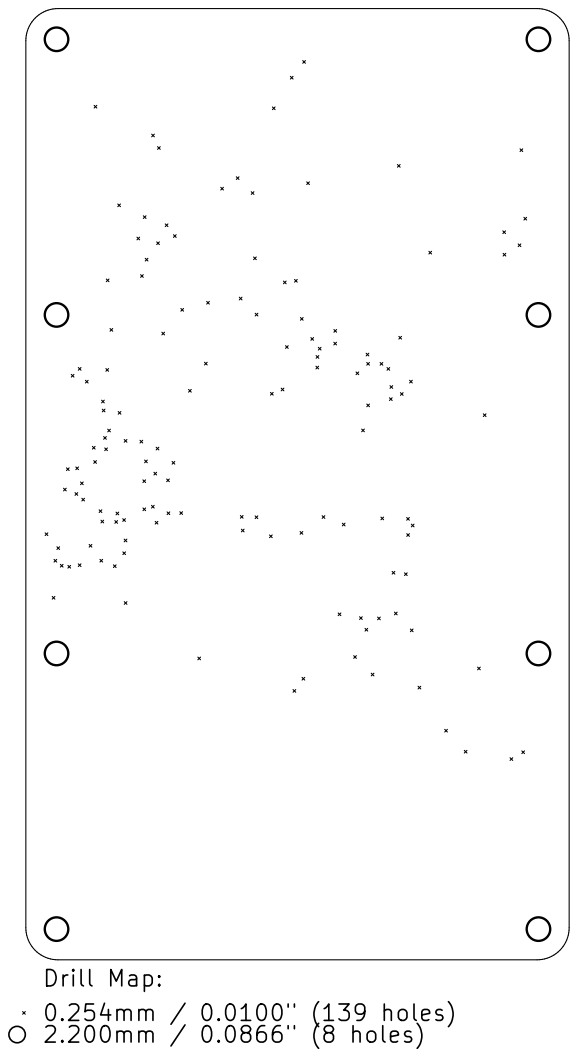
[picture p69: page 1]
