devinhorowitz/solar-business-card/Generated/panel/gerbers/solar-glow-drh-v4_0-panel-PTH_drill_map.pdf

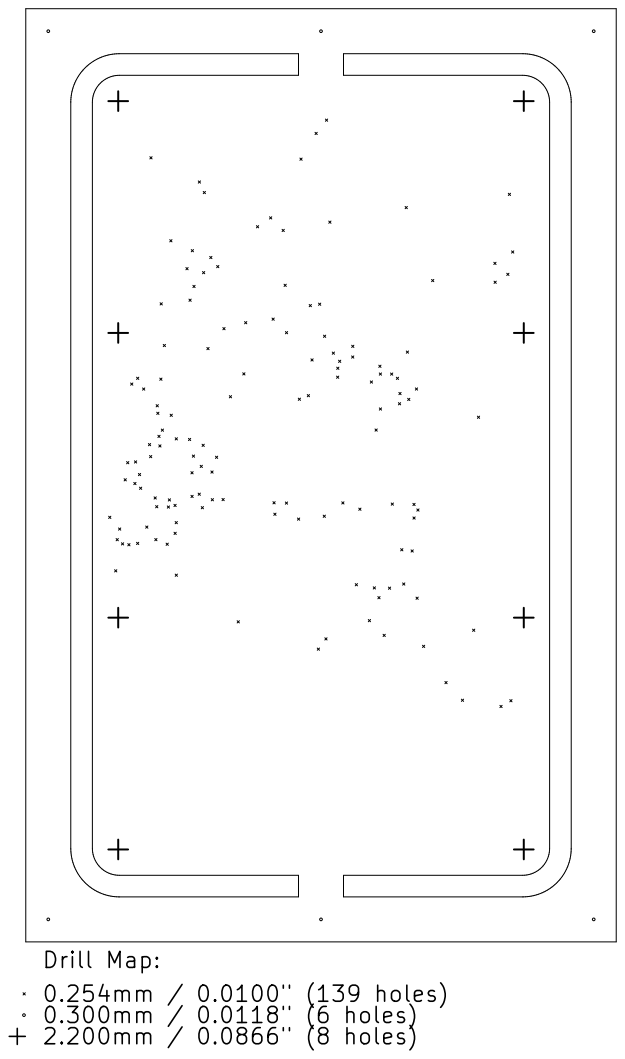
[picture p70: page 1]
