devinhorowitz/solar-business-card/firmware/twi.h

/*
 * twi.h  --  minimal blocking TWI0 host (I2C master) for SOLAR-GLOW DRH.
 *
 * Header-only. One bus (ADXL367 accel @ 0x1D + NT3H tag @ 0x55 + MB85RC512TY FRAM @ 0x50), low speed, no IRQ,
 * no smart mode. Pins are PC2/SDA + PC3/SCL via PORTMUX.TWIROUTEA = ALT2
 * (set in main, not here). External 4.7k pull-ups to VS are fitted, so the
 * internal pull-ups are left off.
 *
 * Bus timing: F_CPU = 1 MHz, target ~100 kHz. The SCL divider has a floor of
 * 10 CLK_PER, so MBAUD = 0 gives 1 MHz / 10 = ~100 kHz (the datasheet's SCL
 * equation carries a rise-time term, so the real bus runs a few percent under
 * that with the 4.7k pulls -- "exactly" here until 2026-08-01 overstated; same
 * bus speed as the old 4 MHz build, which used MBAUD = 15). ~100 kHz is also the
 * ceiling at this clock; 400 kHz fast-mode would need a faster CLK_PER. All
 * transactions are polled; every wait is DOUBLY bounded -- a bus-error /
 * arbitration escape for flagged faults, and a spin budget (TWI_SPIN_MAX) for
 * the un-flagged wedge: a client stretching SCL low forever. The MCTRLA
 * inactive-bus TIMEOUT can NOT bound that case -- per the datasheet (27.5,
 * MCTRLA.TIMEOUT) it is SMBus bus-FREE detection: it only moves the bus state
 * to Idle, sets no MSTATUS flag a wait could see, and a stretched-low SCL is
 * not an "inactive" (idle-high) bus in the first place. It is kept enabled for
 * what it does do: un-sticking the Busy->Idle state so a new transaction can
 * start after a glitch. The stretch hazard is real on this bus -- the NT3H2211
 * stretches by POR default, and NXP warns an interrupted read can leave it
 * stretching "infinitely" -- and before the spin bound it meant a hang: fatal
 * pre-WDT (init/provisioning run before the watchdog is armed, and harvested
 * light can power a spinning core indefinitely), an 8 s WDT reset after.
 *
 * Return convention: 0 = OK, non-zero = fault (NACK or bus error). Callers
 * treat any non-zero as "accel not talking" and skip gracefully.
 */
#ifndef TWI_H
#define TWI_H

#include <avr/io.h>
#include <stdint.h>
#include "board.h"          /* F_CPU (for util/delay) + the pin map */
#include <util/delay.h>

#define TWI_MBAUD_100K  0    /* 1 MHz / (10 + 2*0) = 100 kHz @ F_CPU = 1 MHz */

/* Spin budget for the polled MSTATUS waits (see header note): the escape for a
 * clock-stretching client, which sets NO flag and would otherwise spin forever.
 * One twi_wait() iteration is 10 cycles at -Os (LDS+MOV+AND+BRNE+SUBI+SBC+BRNE,
 * disassembly-verified), so 8192 spins ~ 82 ms at 1 MHz -- orders beyond any legitimate
 * transfer (a byte is ~90 us) or NT3H RF-arbitration stretch (~ms), and far
 * under the 8.0 s watchdog (WDT.CTRLA PERIOD = 0xB, 8KCLK = 8.0 s per the
 * DS40002443 WDT PERIOD table -- NOT the 8.192 s an earlier note here assumed)
 * even across a multi-wait transaction chain. On
 * expiry the wait reports a plain fault: the caller STOPs and skips, and a
 * still-stretched bus just faults each later transaction the same bounded way
 * -- degraded, never hung. */
#define TWI_SPIN_MAX    8192u

/* Bounded wait for any flag in `bits` (RIF/WIF/BUSERR/ARBLOST): returns the
 * MSTATUS snapshot that satisfied it, or 0 on spin-budget expiry. Callers must
 * still inspect the snapshot -- error flags can arrive TOGETHER with WIF (the
 * datasheet sets WIF alongside ARBLOST/BUSERR, and RXACK is only valid when
 * both are clear), so "the wait ended" never by itself means "success". */
static inline uint8_t twi_wait(uint8_t bits)
{
    for (uint16_t spin = TWI_SPIN_MAX; spin; spin--) {
        uint8_t st = TWI0.MSTATUS;
        if (st & bits) return st;
    }
    return 0;
}

/* ---- SDA/SCL as plain GPIO, for the pre-enable bus recovery below ----
 * TWI0 ALT2 routing (PORTMUX.TWIROUTEA, set in main): SDA = PC2, SCL = PC3.
 * While TWI0.MCTRLA.ENABLE is 0 the pins are ordinary PORT pins, which is what
 * makes the recovery possible at all. Open-drain is emulated the only correct
 * way on a shared bus: never drive HIGH (that would fight a target holding the
 * line), only drive LOW or release to input and let the 4.7k pull-ups lift it. */
#define TWI_SDA_bm   PIN2_bm
#define TWI_SCL_bm   PIN3_bm
#define TWI_PORT     PORTC
#define TWI_HALF_US  5            /* 5 us half-period = 100 kHz recovery clock */

/* Recover a bus wedged with SDA held LOW by a target mid-transaction.
 *
 * The reachable cause on this card is our OWN reset: a watchdog reset (or a
 * brownout, or a UPDI attach) that lands while a target is clocking out a byte
 * leaves that target still driving SDA low, waiting for clocks that will never
 * come -- and the TWI host cannot issue a START on a bus whose SDA is already
 * low, so every transaction fails forever. The accel is the card's only input,
 * so "forever" means a dead card that still boots and still polls.
 *
 * The I2C-bus spec's recovery (UM10204 sec 3.1.16) is up to 9 SCL pulses, which
 * walks the stuck target through the rest of its byte until it releases SDA at
 * an ACK slot, followed by a STOP to resynchronise every target's state machine.
 * Cheap and safe to run unconditionally-when-needed at init: if SDA is already
 * high (the normal case) this does nothing at all. */
static inline void twi_bus_clear(void)
{
    /* Release both lines to inputs first; the pull-ups define the idle state. */
    TWI_PORT.DIRCLR = TWI_SDA_bm | TWI_SCL_bm;
    TWI_PORT.OUTCLR = TWI_SDA_bm | TWI_SCL_bm;   /* drive LOW when DIR is set */
    _delay_us(TWI_HALF_US);

    if (TWI_PORT.IN & TWI_SDA_bm)
        return;                                  /* SDA idle high -> nothing wedged */

    for (uint8_t i = 0; i < 9 && !(TWI_PORT.IN & TWI_SDA_bm); i++) {
        TWI_PORT.DIRSET = TWI_SCL_bm;            /* SCL low  */
        _delay_us(TWI_HALF_US);
        TWI_PORT.DIRCLR = TWI_SCL_bm;            /* SCL released -> pulled high */
        _delay_us(TWI_HALF_US);
    }

    /* STOP, with SDA taken low UNDER A LOW SCL first. The old order pulled SDA
     * low while SCL was already high -- which IS a START condition -- and then
     * released it, i.e. START immediately followed by STOP, the sequence the EA
     * datasheet itself names an illegal bus operation (audit (e)). Benign for
     * these three targets in practice, but a recovery routine has no business
     * emitting undefined bus states at the exact moment a target is confused.
     * Correct order: SCL low (SDA moves under a low clock are data, never
     * START/STOP), then SDA low, then SCL high, then SDA low->high under the
     * high clock = one clean STOP and nothing else. */
    TWI_PORT.DIRSET = TWI_SCL_bm;                /* SCL low: SDA may now move freely */
    _delay_us(TWI_HALF_US);
    TWI_PORT.DIRSET = TWI_SDA_bm;                /* SDA low, no START implied */
    _delay_us(TWI_HALF_US);
    TWI_PORT.DIRCLR = TWI_SCL_bm;                /* SCL released -> high */
    _delay_us(TWI_HALF_US);
    TWI_PORT.DIRCLR = TWI_SDA_bm;                /* SDA low -> high under SCL high = STOP */
    _delay_us(TWI_HALF_US);
}

static inline void twi_init(void)
{
    /* Clear a stuck bus BEFORE handing the pins to TWI0 -- the peripheral has no
     * way to do this itself, and a wedged SDA would otherwise fault every
     * transaction for the life of the power cycle. */
    twi_bus_clear();

    TWI0.MBAUD   = TWI_MBAUD_100K;
    /* Host on. The inactive-bus timeout does NOT rescue a hung wait (see the
     * header note -- that is what TWI_SPIN_MAX is for); it is enabled because it
     * DOES auto-return the bus-state machine to Idle after a disturbance, so a
     * transaction that faulted can be retried without a manual state poke. */
    TWI0.MCTRLA  = TWI_TIMEOUT_200US_gc | TWI_ENABLE_bm;
    TWI0.MSTATUS = TWI_BUSSTATE_IDLE_gc;      /* force bus state to IDLE */
}

/* address phase. read=0 write, read=1 read. returns 0 ok, 1 fault. */
static inline uint8_t twi_start(uint8_t addr7, uint8_t read)
{
    uint8_t st;
    TWI0.MADDR = (uint8_t)((addr7 << 1) | (read & 1u));
    if (read) {
        /* The address phase is a WRITE regardless of direction: if no device
         * ACKs, WIF (not RIF) is set together with RXACK. Wait on WIF/BUSERR/
         * ARBLOST here too -- RIF and WIF are mutually exclusive, so anything
         * but RIF (or a spin expiry, st = 0) is an address-NACK / fault. */
        st = twi_wait(TWI_RIF_bm | TWI_WIF_bm | TWI_BUSERR_bm | TWI_ARBLOST_bm);
        if (!(st & TWI_RIF_bm)) return 1;
    } else {
        st = twi_wait(TWI_WIF_bm | TWI_BUSERR_bm | TWI_ARBLOST_bm);
        if (!(st & TWI_WIF_bm) || (st & (TWI_BUSERR_bm | TWI_ARBLOST_bm)))
            return 1;                     /* wedge (st=0), bus error, or arb lost
                                           * (RXACK is not valid on those) */
        if (st & TWI_RXACK_bm) return 1;  /* address NACKed */
    }
    return 0;
}

/* write one data byte. returns 0 ok (ACK), 1 fault (NACK / bus error). */
static inline uint8_t twi_write(uint8_t b)
{
    uint8_t st;
    TWI0.MDATA = b;
    st = twi_wait(TWI_WIF_bm | TWI_BUSERR_bm | TWI_ARBLOST_bm);
    if (!(st & TWI_WIF_bm) || (st & (TWI_BUSERR_bm | TWI_ARBLOST_bm))) return 1;
    return (st & TWI_RXACK_bm) ? 1 : 0;
}

/* read one data byte into *out. ack=1 -> ACK + clock next byte; ack=0 -> NACK
 * + STOP. returns 0 ok, 1 fault (bus error / arb lost). The status is returned
 * separately from the data so a real 0xFF byte is never confused with an error. */
static inline uint8_t twi_read(uint8_t ack, uint8_t *out)
{
    uint8_t st = twi_wait(TWI_RIF_bm | TWI_BUSERR_bm | TWI_ARBLOST_bm);
    if (!(st & TWI_RIF_bm) || (st & (TWI_BUSERR_bm | TWI_ARBLOST_bm))) return 1;
    *out = TWI0.MDATA;
    if (ack) TWI0.MCTRLB = TWI_MCMD_RECVTRANS_gc;                 /* ACK, go again */
    else     TWI0.MCTRLB = TWI_ACKACT_bm | TWI_MCMD_STOP_gc;      /* NACK + STOP   */
    return 0;
}

/* read the FINAL data byte with an ACK, then STOP -- the NT3H2211's drawn last-byte
 * handshake (its Figures 18/19 and their prose have the host ACK the last byte:
 * "the bus master/host will acknowledge it and issue a Stop condition"), which is a
 * PER-DEVICE convention, not the universal NACK-last: the FRAM's own figures draw
 * NACK-last, so fram.c keeps twi_read(0,..). Safe only for fixed-length reads where
 * the target ends transmission on its own count. ACKACT=0 (ACK) + MCMD_STOP sends
 * the ACK and then the STOP in one command. returns 0 ok, 1 fault. */
static inline uint8_t twi_read_last_ack(uint8_t *out)
{
    uint8_t st = twi_wait(TWI_RIF_bm | TWI_BUSERR_bm | TWI_ARBLOST_bm);
    if (!(st & TWI_RIF_bm) || (st & (TWI_BUSERR_bm | TWI_ARBLOST_bm))) return 1;
    *out = TWI0.MDATA;
    TWI0.MCTRLB = TWI_MCMD_STOP_gc;               /* ACK (ACKACT=0) + STOP */
    return 0;
}

static inline void twi_stop(void)
{
    TWI0.MCTRLB = TWI_MCMD_STOP_gc;
}

/* write one register. returns 0 ok, 1 fault. */
static inline uint8_t twi_reg_write(uint8_t addr7, uint8_t reg, uint8_t val)
{
    if (twi_start(addr7, 0)) { twi_stop(); return 1; }
    if (twi_write(reg))      { twi_stop(); return 1; }
    if (twi_write(val))      { twi_stop(); return 1; }
    twi_stop();
    return 0;
}

/* read n registers starting at reg into dst. burst (n>1) sets sub-addr bit7, an
 * ST/LIS2DH12 auto-increment convention. NOTE: the ADXL367 does NOT use bit7 (it
 * auto-increments natively), so a multi-byte read of the accel would send the wrong
 * sub-address -- the accel driver only reads single bytes, so this never bites.
 * returns 0 ok, 1 fault. */
static inline uint8_t twi_reg_read(uint8_t addr7, uint8_t reg, uint8_t *dst, uint8_t n)
{
    if (n == 0) return 0;
    if (twi_start(addr7, 0))                          { twi_stop(); return 1; }
    if (twi_write((n > 1) ? (uint8_t)(reg | 0x80) : reg)) { twi_stop(); return 1; }
    if (twi_start(addr7, 1))                          { twi_stop(); return 1; }  /* repeated start */
    for (uint8_t i = 0; i < n; i++)
        if (twi_read((uint8_t)(i < (n - 1)), &dst[i])) {  /* ACK all but last; last NACKs + STOPs */
            twi_stop();                                   /* bus fault: STOP so the target can't clock-stretch (dst not trustworthy) */
            return 1;
        }
    return 0;
}

#endif /* TWI_H */
